evagorac/Terry/Assemblies/gasSpring.sldasm

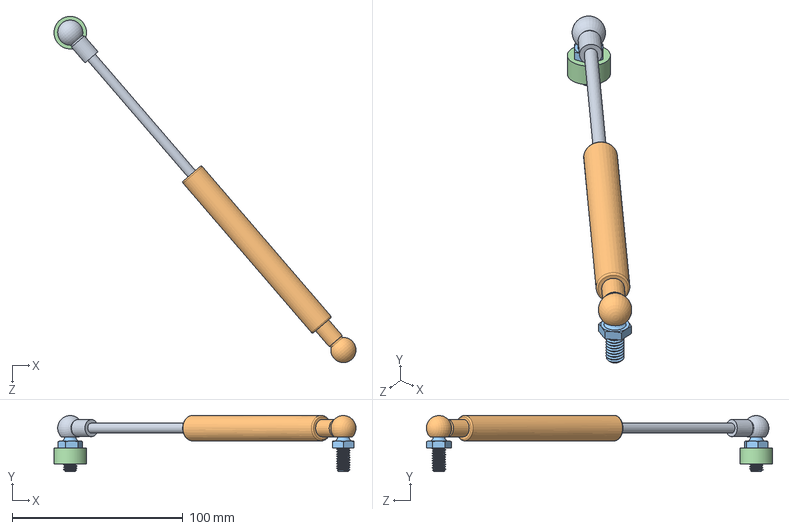
[picture p21: CAD file, 2020-08-20]
Assemblies/gasSpring.sldasm
176.8 x 33.0 x 202.7 mm
Combine2
Combine3
Combine1 x 2
92510A794_ALUM UNTHRD SPACER
