evagorac/Terry/Assemblies/TensionPillarJ4.sldasm

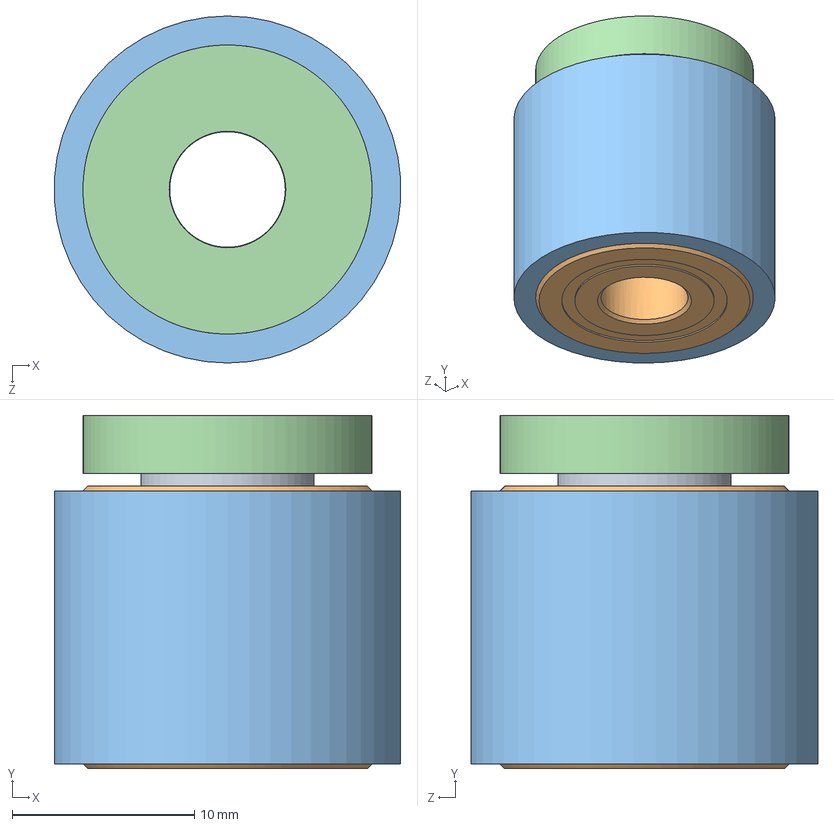
[picture p22: CAD file, 2020-08-20]
Assemblies/TensionPillarJ4.sldasm
19.0 x 19.4 x 19.1 mm
98019A228_MIL SPEC. 300 SERIES SS FLAT WASHER
60355K701_BALL BEARING x 2
Roller^TensionPillarJ4
92510A483_ALUM UNTHRD SPACER
