evagorac/Terry/Assemblies/gasSpring2.sldasm

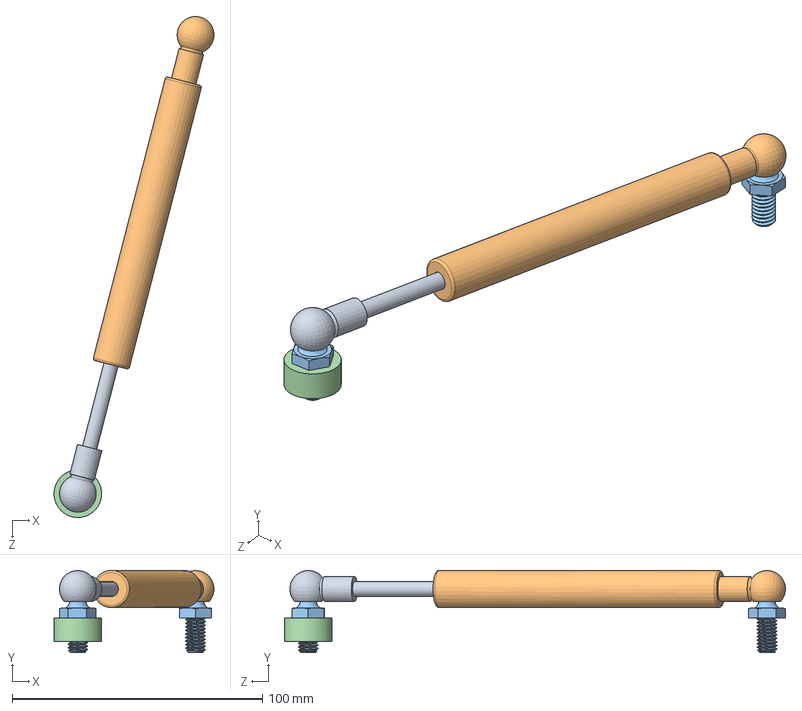
[picture p23: CAD file, 2020-08-20]
Assemblies/gasSpring2.sldasm
64.0 x 33.0 x 200.3 mm
Combine2
Combine3
Combine1 x 2
92510A794_ALUM UNTHRD SPACER
