evagorac/Terry/Parts/Pulleys/PulleyHubbed.SLDASM

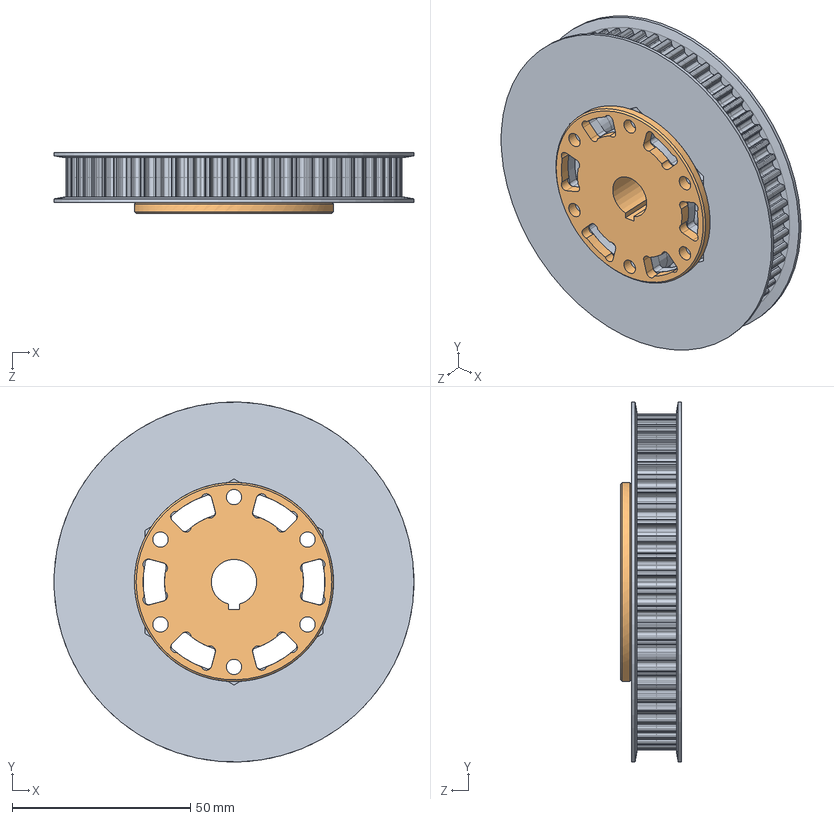
[picture p24: CAD file, 2020-08-20]
Parts/Pulleys/PulleyHubbed.SLDASM
101.0 x 101.0 x 17.2 mm
217-3200-001 Rev3.step x 2
1_2_ID_1_8_Keyway_Aluminum_VersaHub_217-2590 v1
