evagorac/Terry/Parts/Pulleys/60t_x_18mm_Wide_VersaPulley_Kit_HTD_5mm_VersaKeys_217-3200 v2.SLDASM

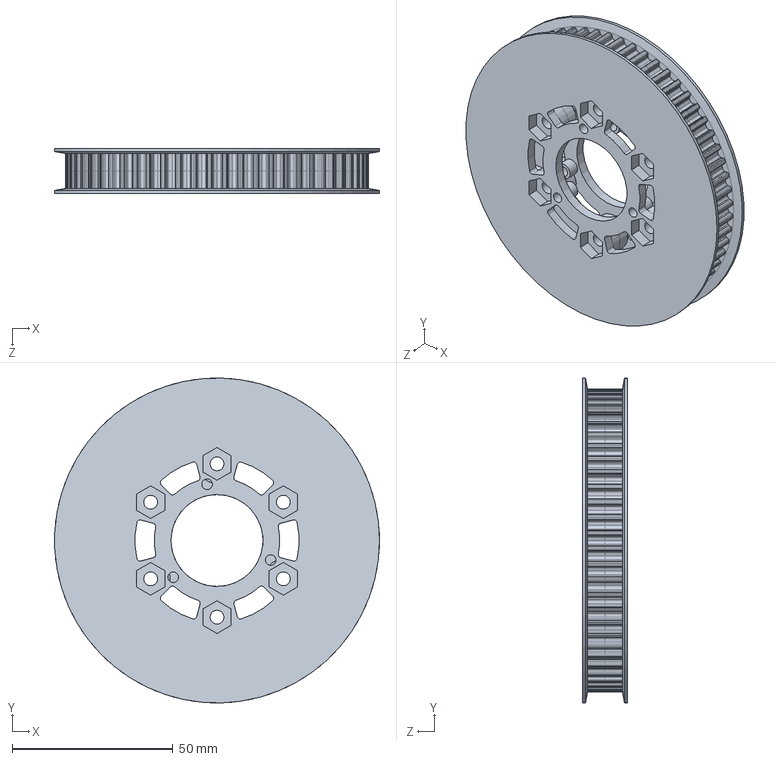
[picture p25: CAD file, 2020-08-20]
Parts/Pulleys/60t_x_18mm_Wide_VersaPulley_Kit_HTD_5mm_VersaKeys_217-3200 v2.SLDASM
101.0 x 101.0 x 14.0 mm
217-3200-001 Rev3.step x 2
