evagorac/Terry/STLS/Done/1MainMiterSpacer^Forearm.STL

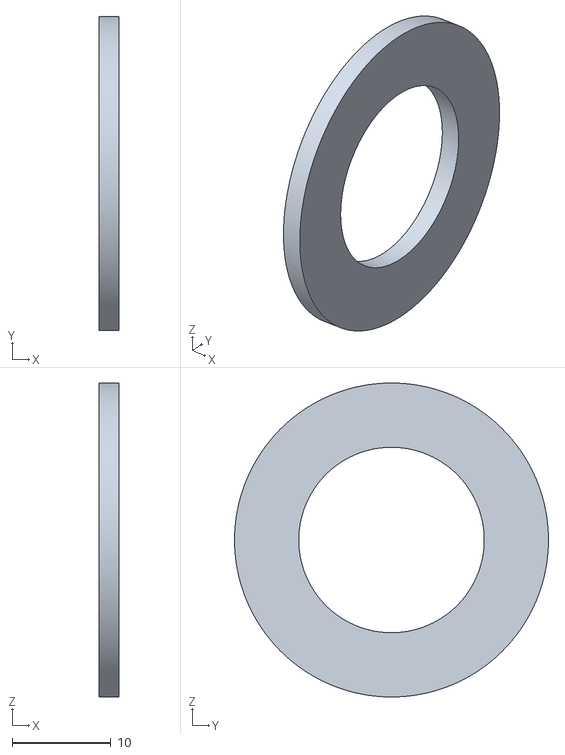
[picture p26: CAD file, 2020-08-20]
STLS/Done/1MainMiterSpacer^Forearm.STL
2.03 x 31.8 x 31.8
