evagorac/Terry/MillParts/Box.sldprt

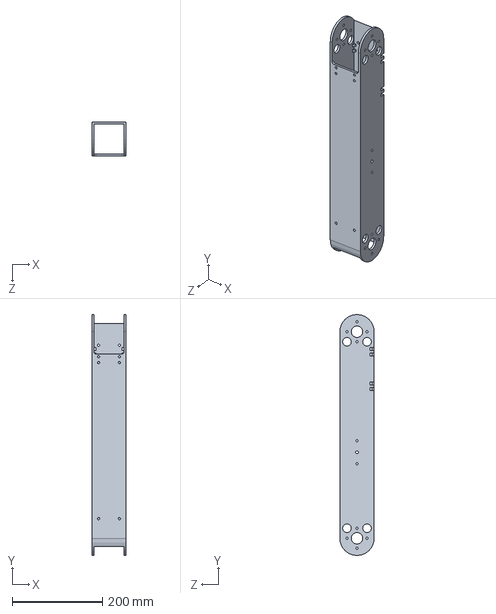
[picture p27: CAD file, 2021-02-25]
MillParts/Box.sldprt
76.2 x 533.4 x 76.2 mm
