evagorac/Terry/Parts/BBQ Bearing/8in.SLDPRT

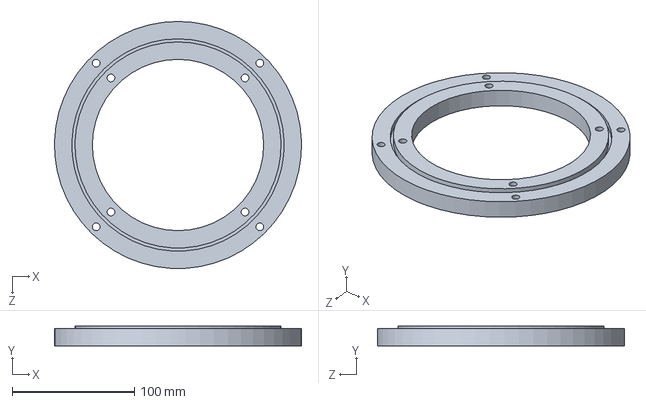
[picture p28: CAD file, 2020-08-20]
Parts/BBQ Bearing/8in.SLDPRT
201.9 x 16.0 x 202.0 mm
