evagorac/Terry/Parts/Limit/switch.SLDPRT

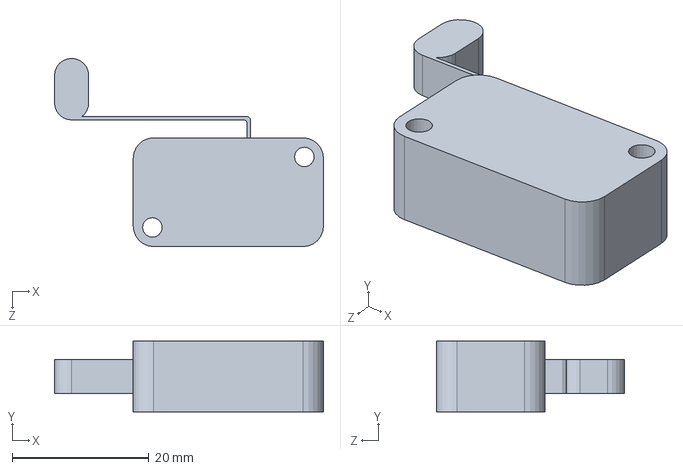
[picture p29: CAD file, 2020-08-20]
Parts/Limit/switch.SLDPRT
39.3 x 10.3 x 27.5 mm
