evagorac/Terry/Parts/MiscBodies/ShaftSupp^Shoulder.sldprt

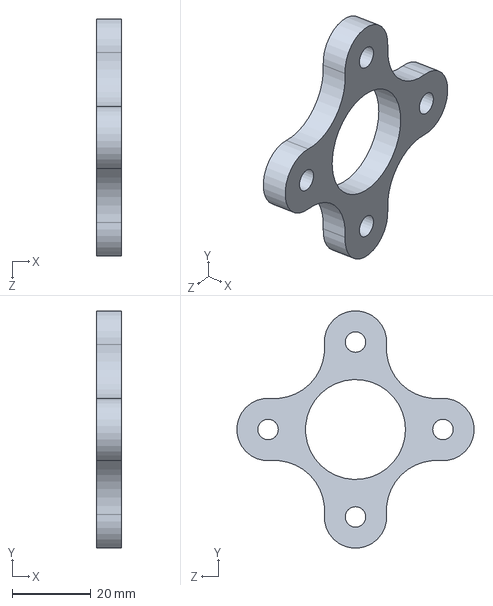
[picture p30: CAD file, 2021-02-25]
Parts/MiscBodies/ShaftSupp^Shoulder.sldprt
6.35 x 60.2 x 60.2 mm
