evagorac/Terry/Parts/Motors/Gearboxes/VersaPlanetary_CIM_Adapter_217-4018.SLDPRT

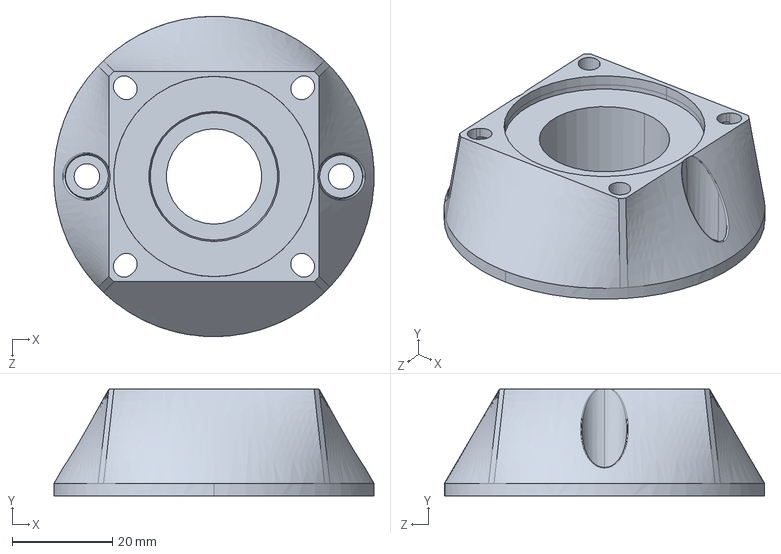
[picture p31: CAD file, 2020-08-20]
Parts/Motors/Gearboxes/VersaPlanetary_CIM_Adapter_217-4018.SLDPRT
63.9 x 21.4 x 64.0 mm
