evagorac/Terry/Parts/Pulleys/PulleyGenerator.SLDPRT

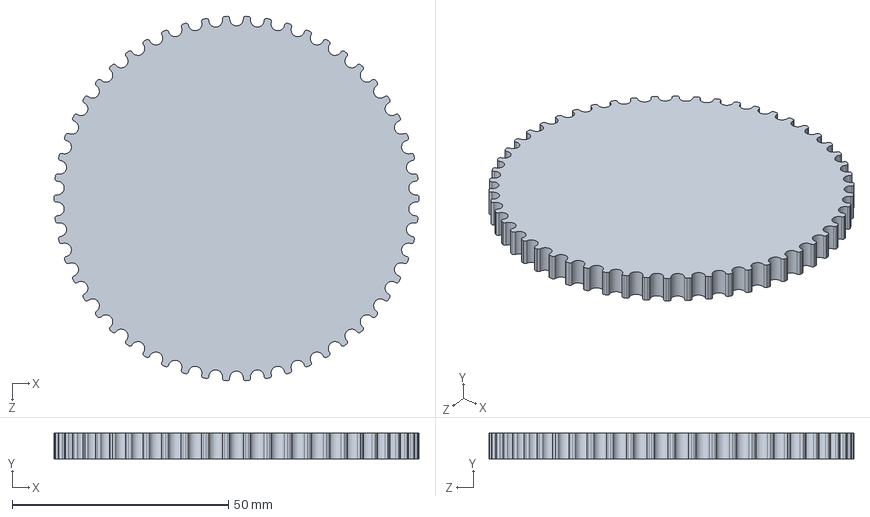
[picture p32: CAD file, 2021-02-25]
Parts/Pulleys/PulleyGenerator.SLDPRT
84.4 x 6.00 x 84.3 mm
