evagorac/Terry/Parts/VersaGussets/VersaFrame_Face_Bearing_Mount_217-4183.SLDPRT

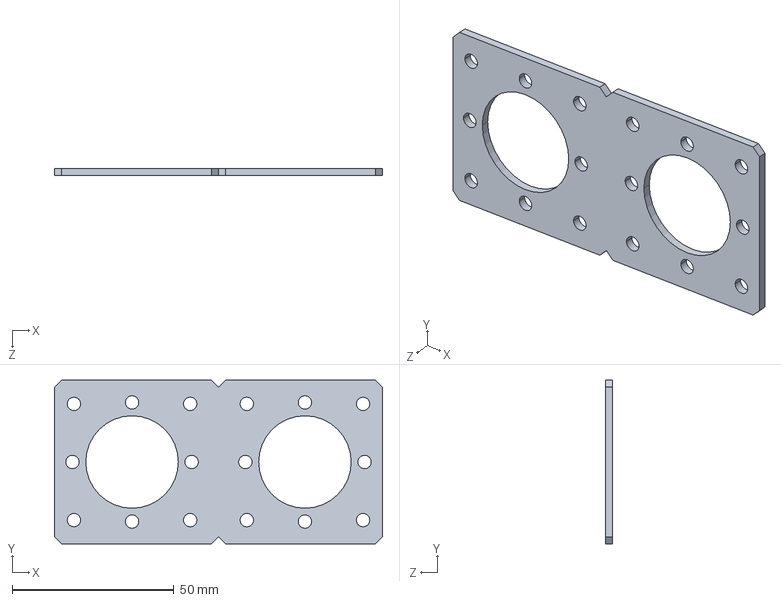
[picture p33: CAD file, 2020-08-20]
Parts/VersaGussets/VersaFrame_Face_Bearing_Mount_217-4183.SLDPRT
101.3 x 50.5 x 2.29 mm
