evagorac/Terry/Plates/Eighth/SidePlate1fix.sldprt

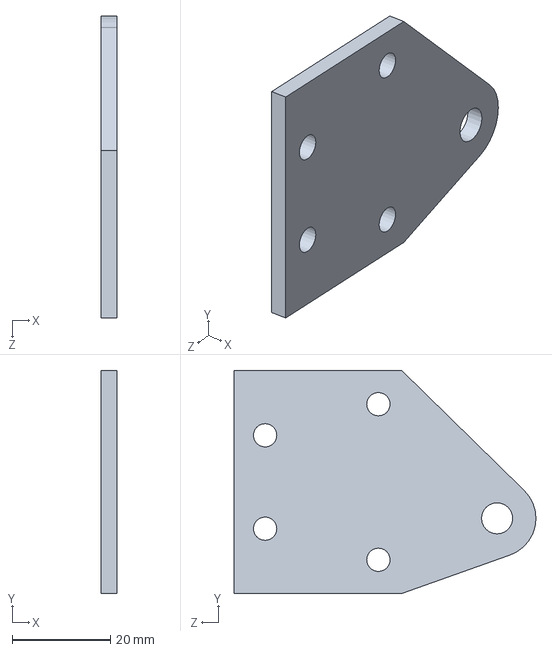
[picture p34: CAD file, 2020-12-14]
Plates/Eighth/SidePlate1fix.sldprt
3.17 x 45.5 x 61.6 mm
