evagorac/Terry/Plates/Quarter/J2Plate.sldprt

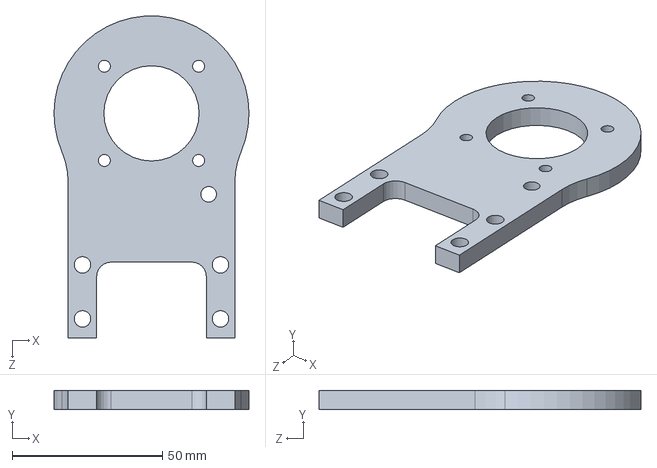
[picture p35: CAD file, 2020-08-20]
Plates/Quarter/J2Plate.sldprt
65.0 x 6.35 x 107.3 mm
