evagorac/Terry/STLS/Done/1Roller^TensionPillarJ3.STL

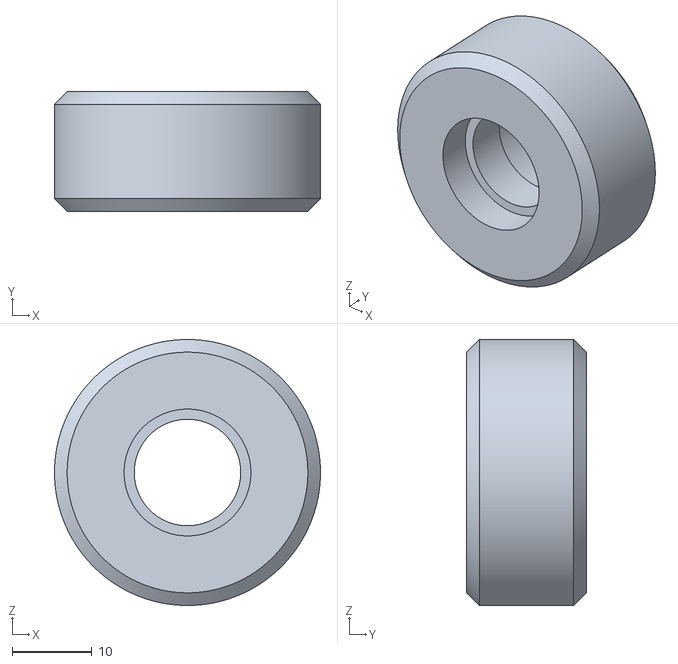
[picture p36: CAD file, 2020-08-20]
STLS/Done/1Roller^TensionPillarJ3.STL
33.3 x 15.0 x 33.3
