evagorac/Terry/STLS/Undone/2WristCover^Forearm.STL

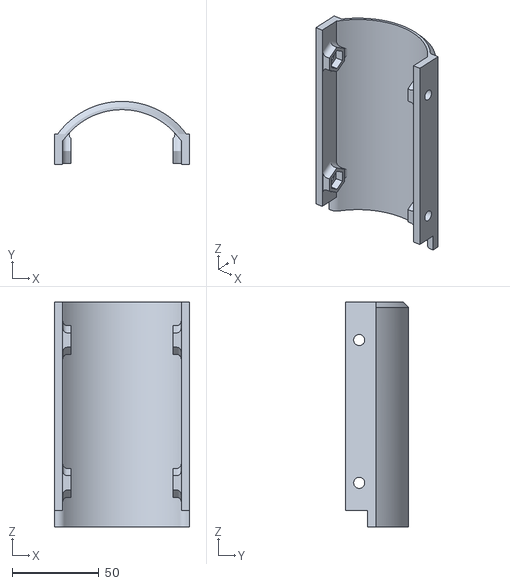
[picture p37: CAD file, 2020-08-20]
STLS/Undone/2WristCover^Forearm.STL
77.8 x 36.3 x 129.5
