evagorac/Terry/MillParts/HandPlate.sldprt

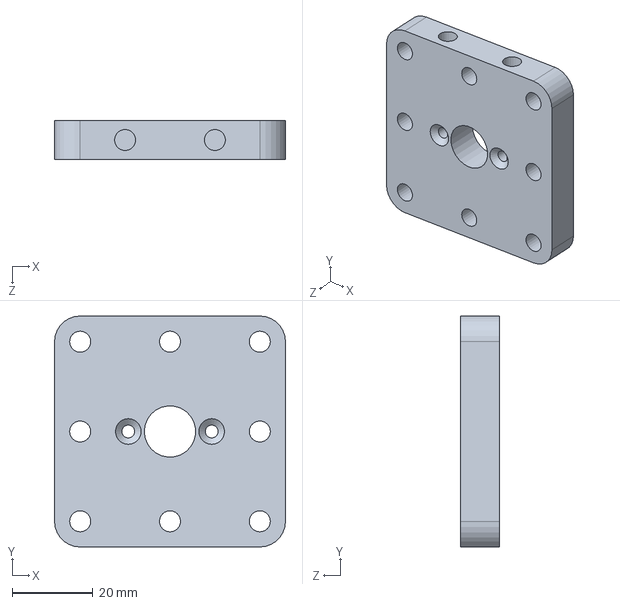
[picture p38: CAD file, 2021-02-25]
MillParts/HandPlate.sldprt
57.1 x 57.1 x 9.53 mm
