evagorac/Terry/Parts/Marker.step

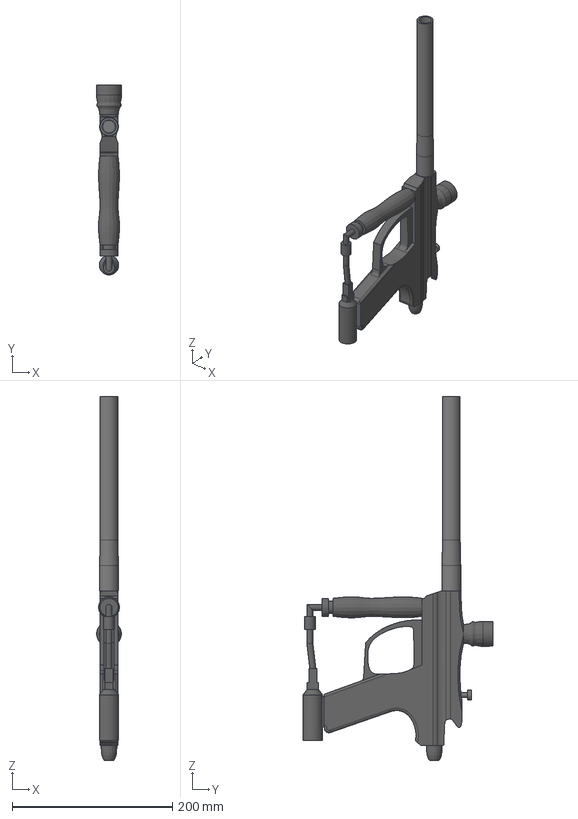
[picture p39: CAD file, 2021-02-25]
Parts/Marker.step
31.0 x 237.2 x 454.7 mm
Barrel
Delarin Bolt
