evagorac/Terry/Parts/MiscBodies/circularLineup.SLDPRT

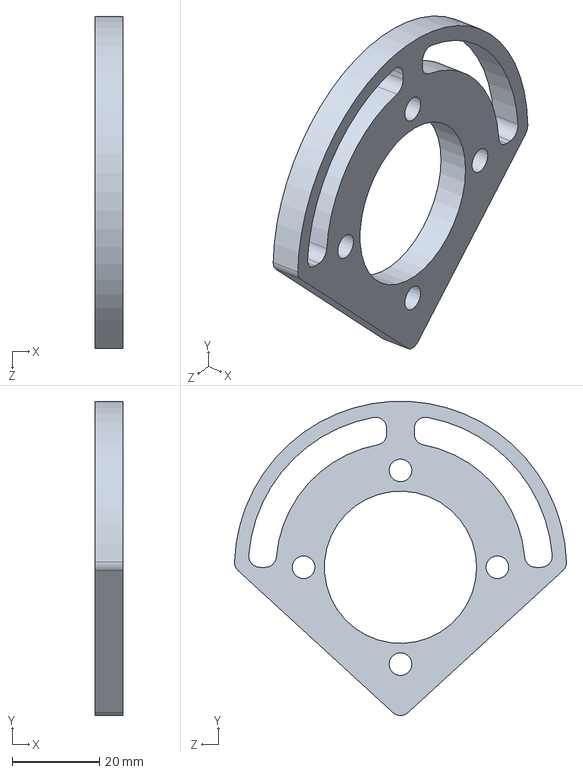
[picture p40: CAD file, 2020-08-20]
Parts/MiscBodies/circularLineup.SLDPRT
6.35 x 72.1 x 76.2 mm
