evagorac/Terry/Parts/Motors/Gearboxes/VersaPlanetary_CIM_Motor_Output_Shaft_Kit_217-2893.SLDPRT

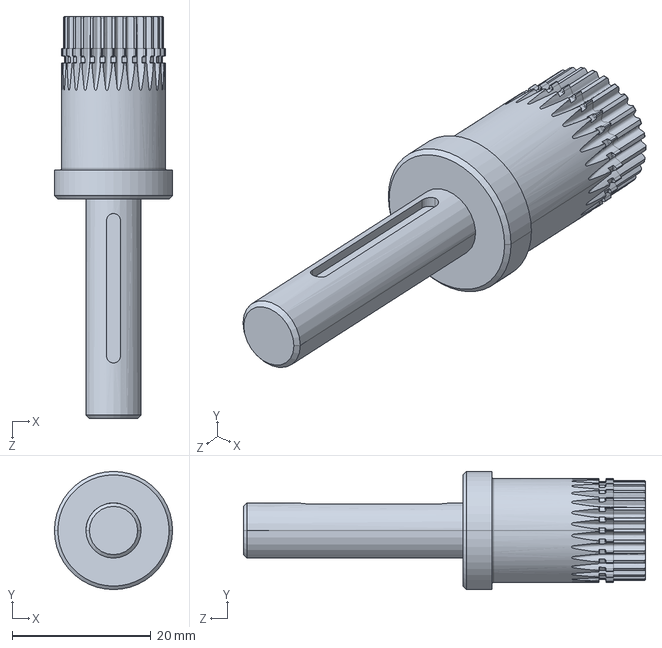
[picture p41: CAD file, 2020-08-20]
Parts/Motors/Gearboxes/VersaPlanetary_CIM_Motor_Output_Shaft_Kit_217-2893.SLDPRT
17.0 x 17.0 x 57.8 mm
