evagorac/Terry/Parts/Pulleys/J1Pulley.SLDPRT

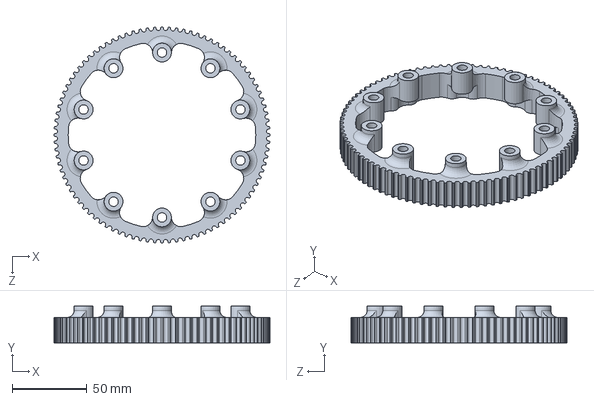
[picture p42: CAD file, 2020-10-19]
Parts/Pulleys/J1Pulley.SLDPRT
144.9 x 24.5 x 144.9 mm
