evagorac/Terry/Parts/Rails/J3MGN12C.sldprt

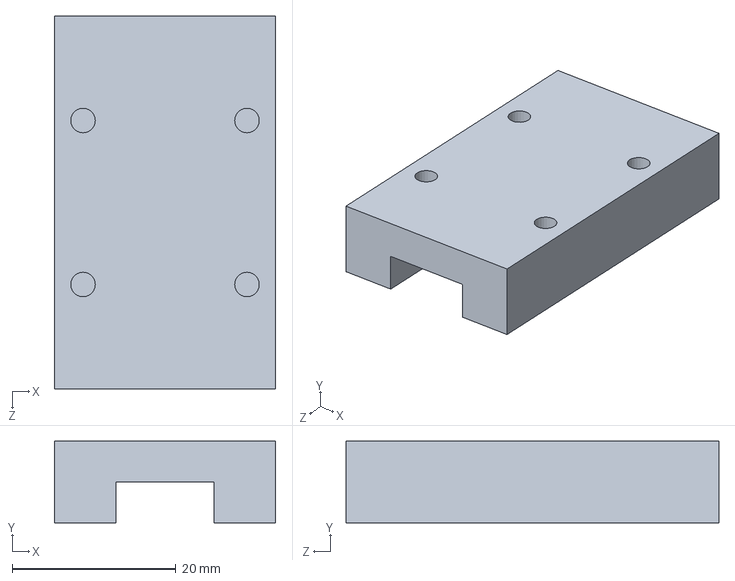
[picture p43: CAD file, 2020-08-20]
Parts/Rails/J3MGN12C.sldprt
27.0 x 10.0 x 45.5 mm
