evagorac/Terry/Plates/Quarter/J3Plate.sldprt

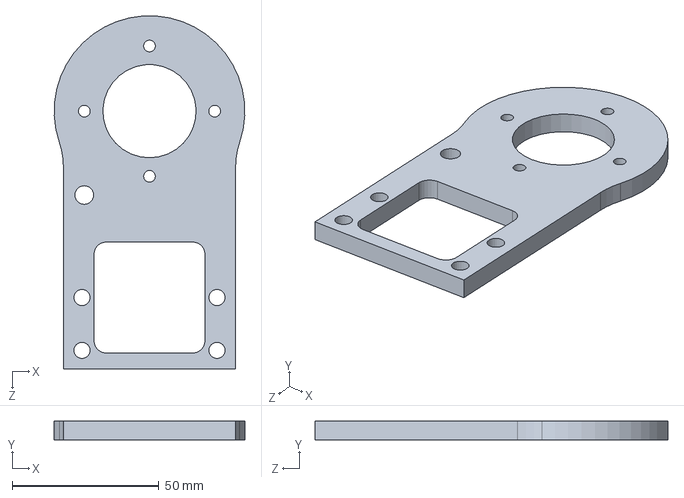
[picture p44: CAD file, 2020-08-20]
Plates/Quarter/J3Plate.sldprt
64.9 x 6.35 x 120.3 mm
