evagorac/Terry/Plates/ThreeEighths/SideTurretPlate.sldprt

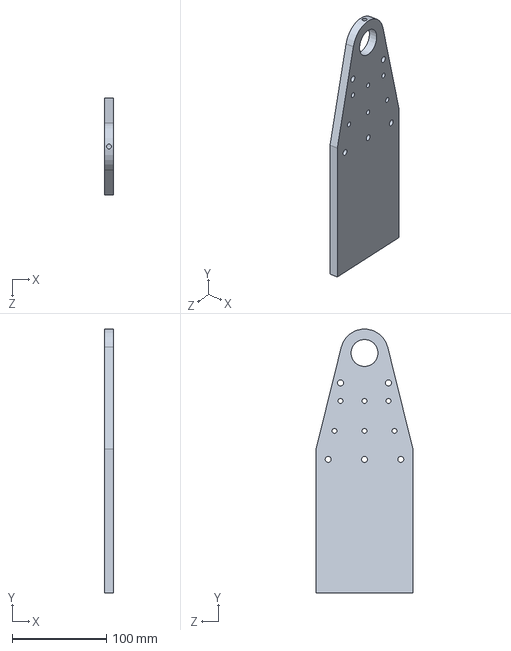
[picture p45: CAD file, 2020-08-20]
Plates/ThreeEighths/SideTurretPlate.sldprt
9.53 x 279.6 x 102.6 mm
