evagorac/Terry/STLS/Done/4Body^192kvMotorEncoded.STL

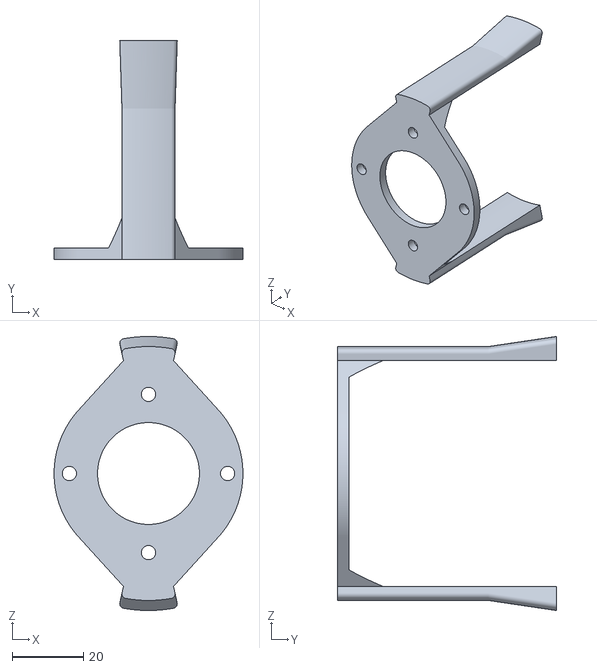
[picture p46: CAD file, 2020-08-20]
STLS/Done/4Body^192kvMotorEncoded.STL
53.0 x 61.4 x 76.9
