evagorac/Terry/Parts/MiscBodies/BigPlateLineup.sldprt

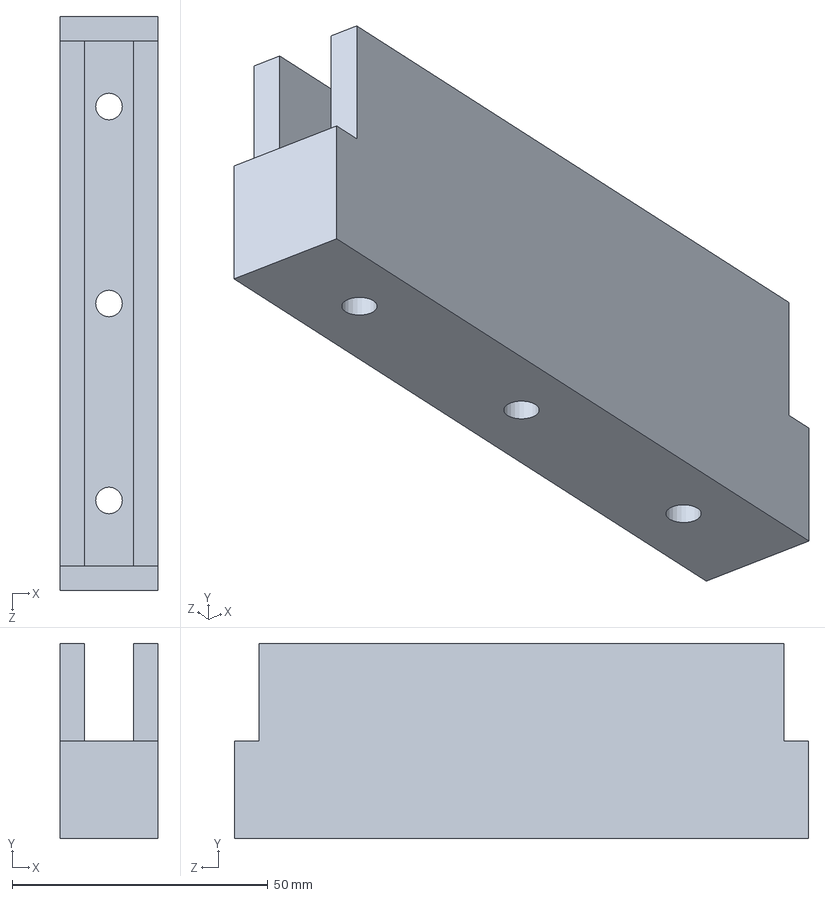
[picture p47: CAD file, 2020-08-20]
Parts/MiscBodies/BigPlateLineup.sldprt
19.0 x 38.1 x 112.1 mm
