evagorac/Terry/Parts/Motors/BetterKEDA.SLDPRT

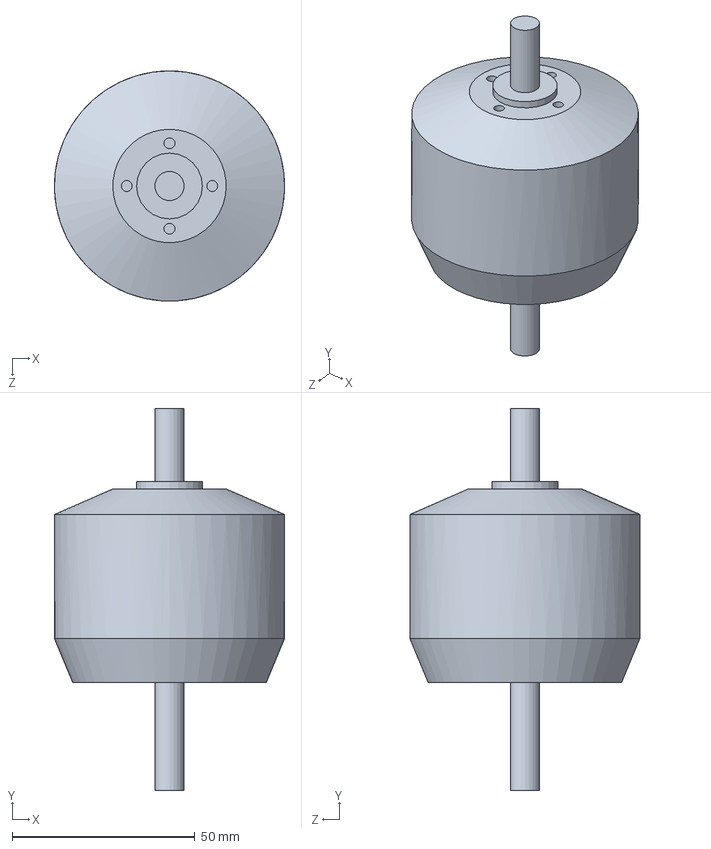
[picture p48: CAD file, 2020-08-20]
Parts/Motors/BetterKEDA.SLDPRT
63.0 x 104.5 x 63.0 mm
