evagorac/Terry/Plates/Eighth/WristSidePlate.sldprt

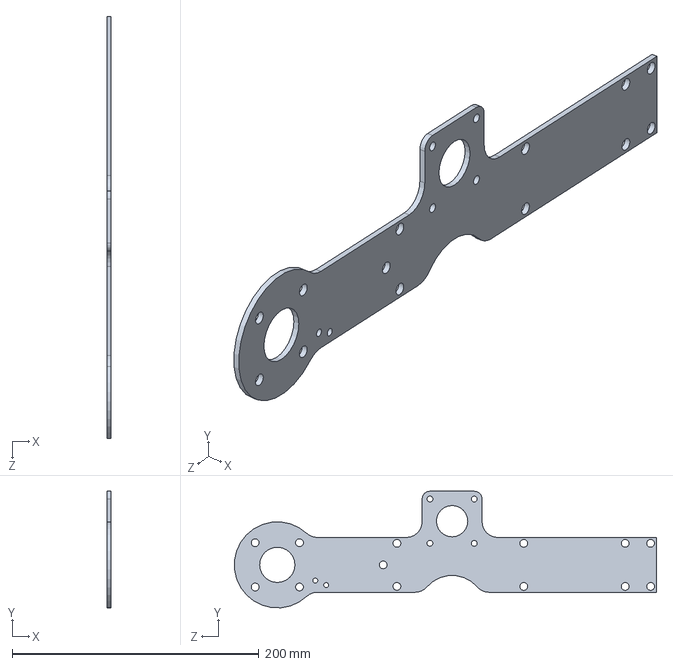
[picture p49: CAD file, 2020-08-20]
Plates/Eighth/WristSidePlate.sldprt
3.18 x 94.5 x 342.1 mm
