evagorac/Terry/Plates/Quarter/BotTurretPlate.sldprt

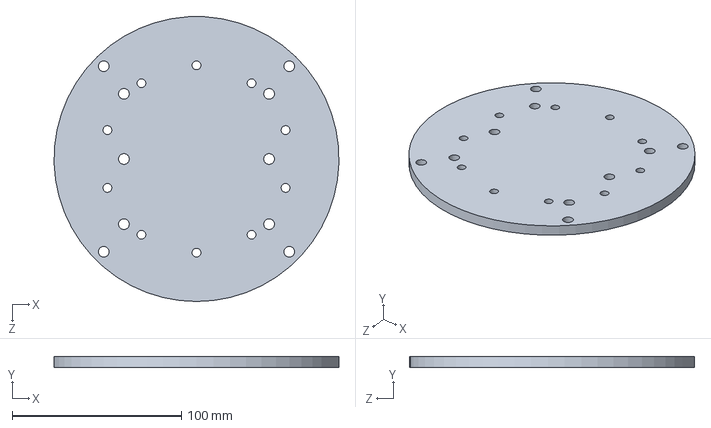
[picture p50: CAD file, 2020-08-20]
Plates/Quarter/BotTurretPlate.sldprt
168.3 x 6.35 x 168.3 mm
