evagorac/Terry/STLS/Done/1ThrustBase^Forearm.STL

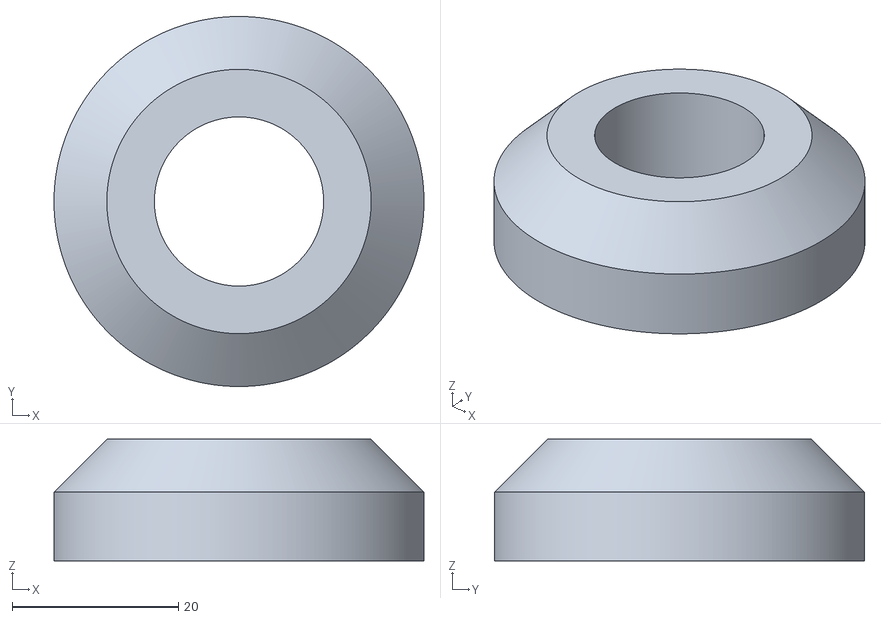
[picture p51: CAD file, 2020-08-20]
STLS/Done/1ThrustBase^Forearm.STL
44.5 x 44.5 x 14.6
