evagorac/Terry/MillParts/WristHub.sldprt

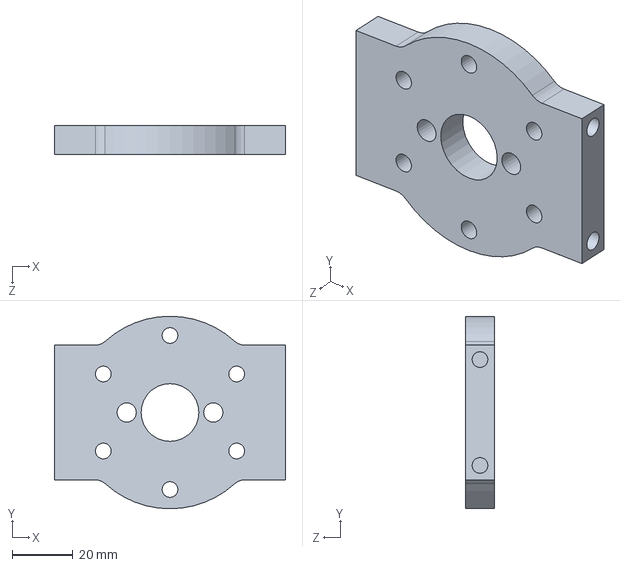
[picture p52: CAD file, 2020-08-20]
MillParts/WristHub.sldprt
76.2 x 63.5 x 9.52 mm
