evagorac/Terry/Parts/Motors/EXTENDED SHAFT KEDA 56-63 195KV Brushless Outrunner 6S 1500W v2 v2.step

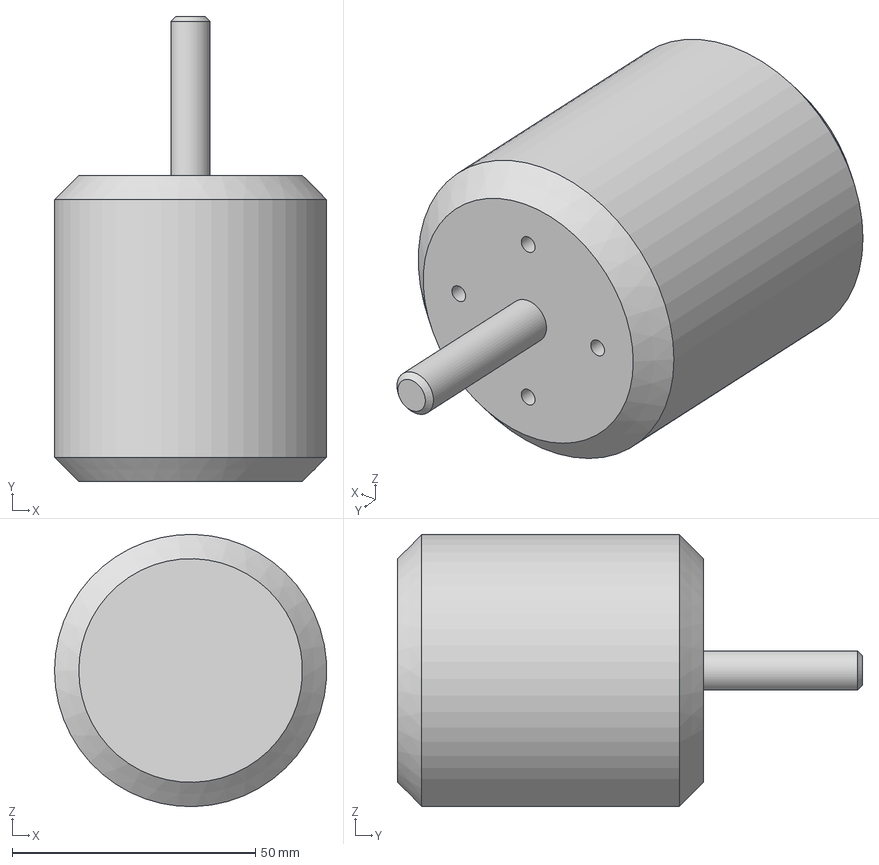
[picture p53: CAD file, 2020-08-20]
Parts/Motors/EXTENDED SHAFT KEDA 56-63 195KV Brushless Outrunner 6S 1500W v2 v2.step
55.9 x 95.7 x 56.0 mm
