evagorac/Terry/Parts/Pulleys/15Tpulley.SLDPRT

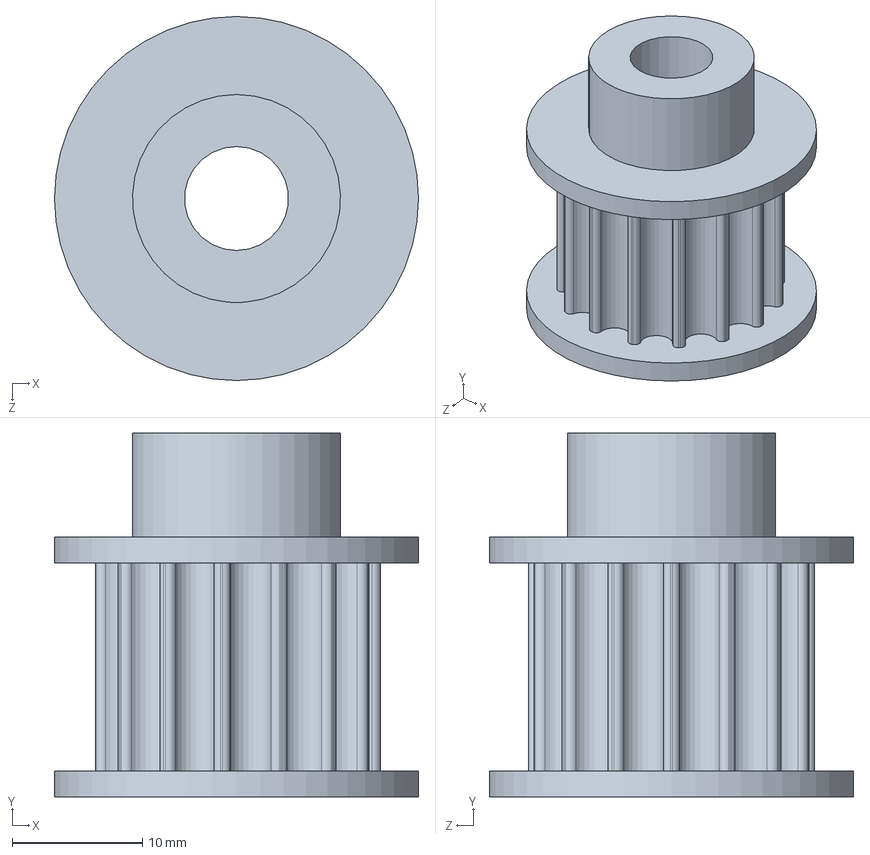
[picture p54: CAD file, 2020-08-20]
Parts/Pulleys/15Tpulley.SLDPRT
28.0 x 28.0 x 28.0 mm
