evagorac/Terry/Plates/Eighth/PulleySupportPlate.sldprt

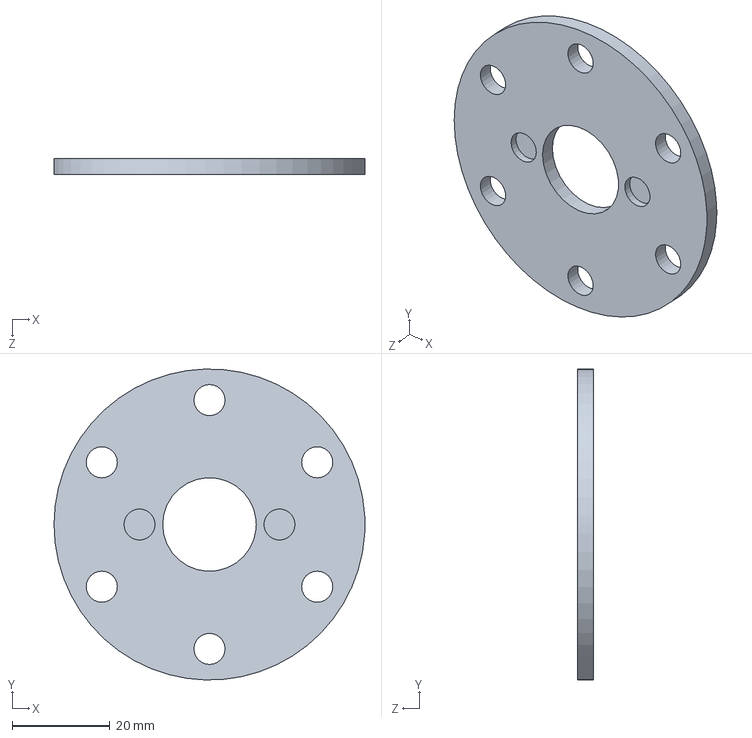
[picture p55: CAD file, 2020-08-20]
Plates/Eighth/PulleySupportPlate.sldprt
63.5 x 63.5 x 3.18 mm
