evagorac/Terry/Plates/Quarter/Sole.sldprt

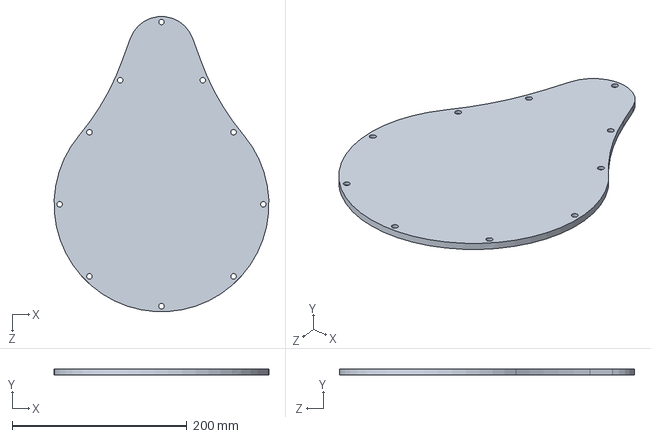
[picture p56: CAD file, 2020-08-20]
Plates/Quarter/Sole.sldprt
245.9 x 6.35 x 338.0 mm
