evagorac/Terry/STLS/Done/1Trigger^Shoulder.STL

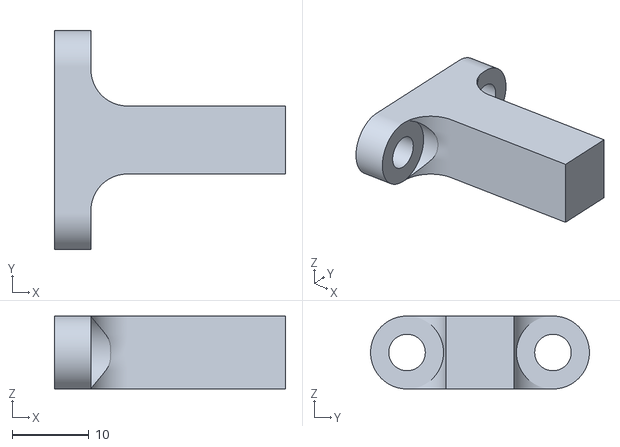
[picture p57: CAD file, 2020-08-20]
STLS/Done/1Trigger^Shoulder.STL
30.2 x 28.6 x 9.53
