evagorac/Terry/Parts/Motors/PROPDRIVE v2 5060 380KV Brushless Outrunner Motor.SLDPRT

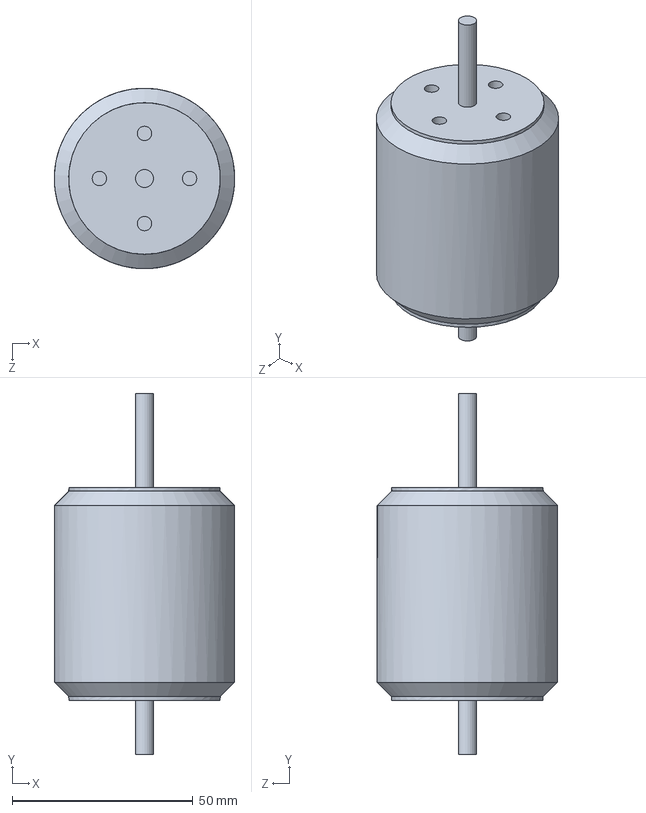
[picture p58: CAD file, 2020-08-20]
Parts/Motors/PROPDRIVE v2 5060 380KV Brushless Outrunner Motor.SLDPRT
50.0 x 100.0 x 50.0 mm
