evagorac/Terry/Parts/Pulleys/1_2_ID_1_8_Keyway_Aluminum_VersaHub_217-2590 v1.SLDPRT

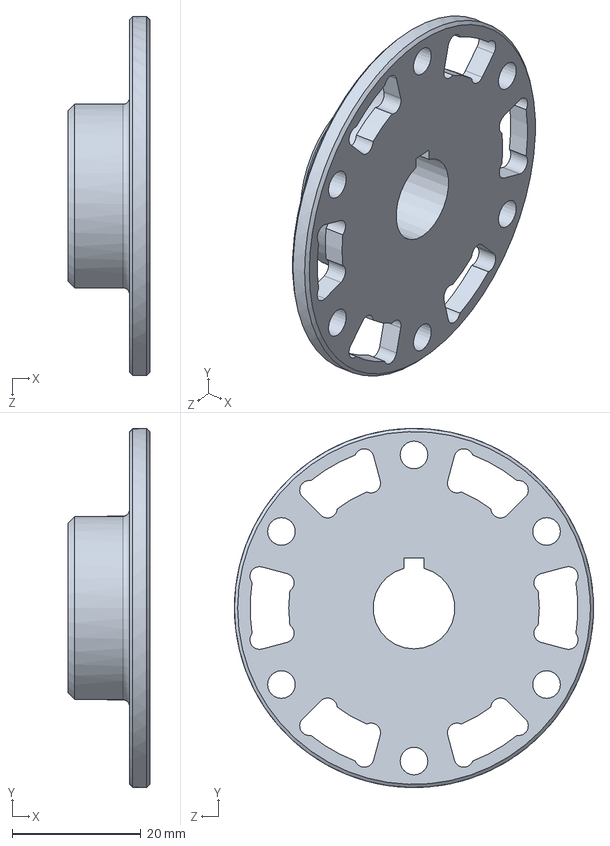
[picture p59: CAD file, 2020-08-20]
Parts/Pulleys/1_2_ID_1_8_Keyway_Aluminum_VersaHub_217-2590 v1.SLDPRT
12.7 x 55.9 x 55.9 mm
