evagorac/Terry/Plates/ThreeEighths/SidePlate.sldprt

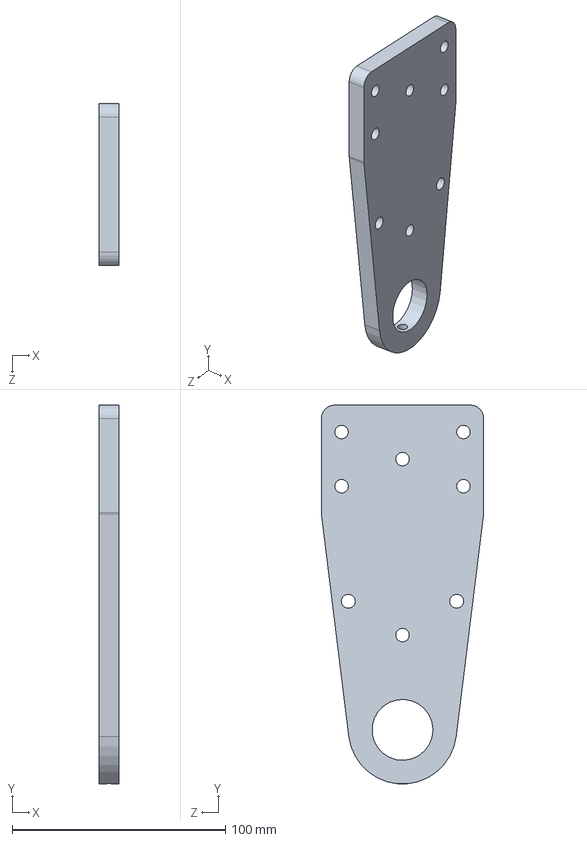
[picture p60: CAD file, 2020-08-20]
Plates/ThreeEighths/SidePlate.sldprt
9.53 x 177.8 x 76.2 mm
