evagorac/Terry/STLS/Done/2BKSpacer^Shoulder.STL

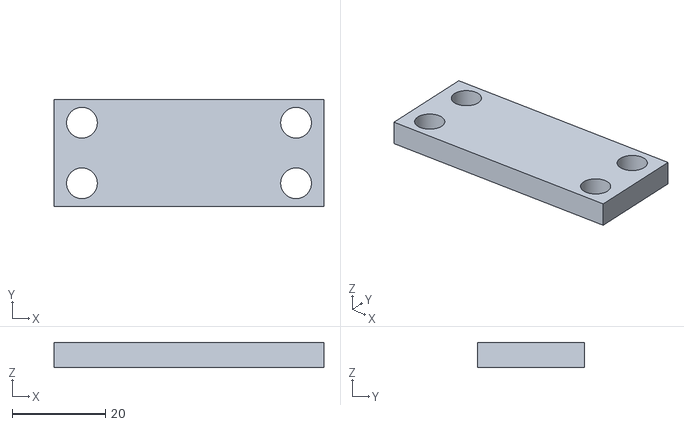
[picture p61: CAD file, 2020-08-20]
STLS/Done/2BKSpacer^Shoulder.STL
58.0 x 23.0 x 5.40
