evagorac/Terry/Parts/Pulleys/30Tpulley.SLDPRT

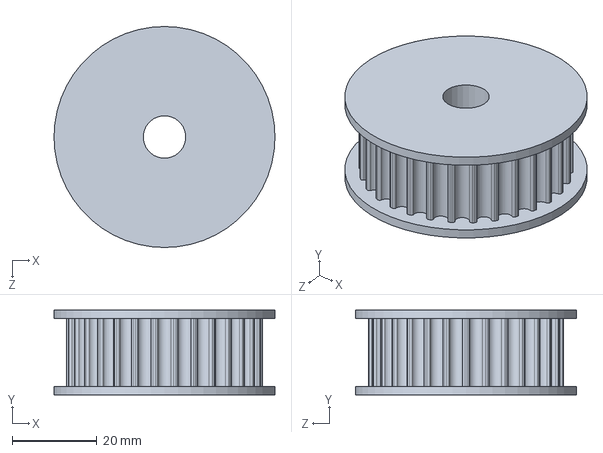
[picture p62: CAD file, 2020-08-20]
Parts/Pulleys/30Tpulley.SLDPRT
52.0 x 20.0 x 52.0 mm
