evagorac/Terry/Plates/Quarter/TopTurretPlate.sldprt

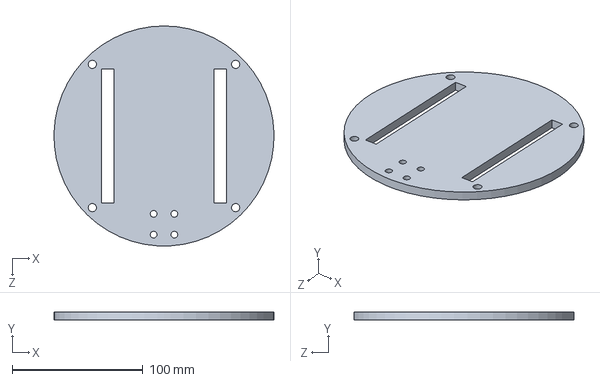
[picture p63: CAD file, 2020-08-20]
Plates/Quarter/TopTurretPlate.sldprt
168.3 x 6.35 x 168.3 mm
