evagorac/Terry/Plates/ThreeEighths/WristHub.sldprt

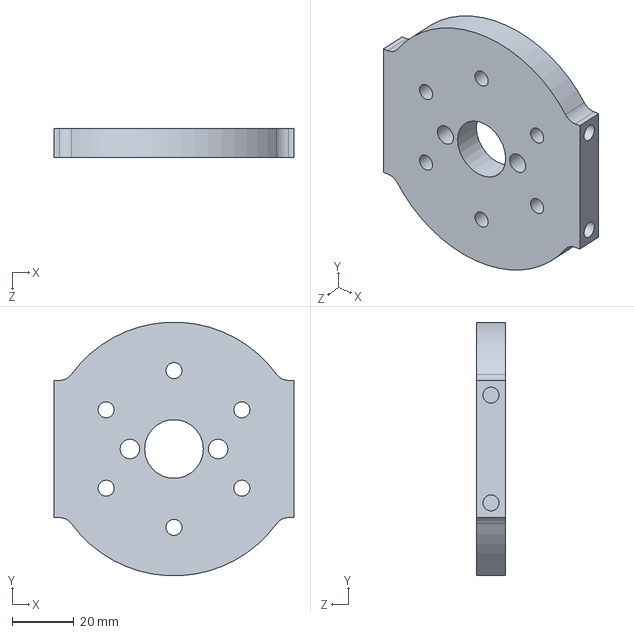
[picture p64: CAD file, 2020-08-20]
Plates/ThreeEighths/WristHub.sldprt
77.8 x 82.1 x 9.53 mm
