evagorac/Terry/STLS/Done/1BotTurretHousing^Base.STL

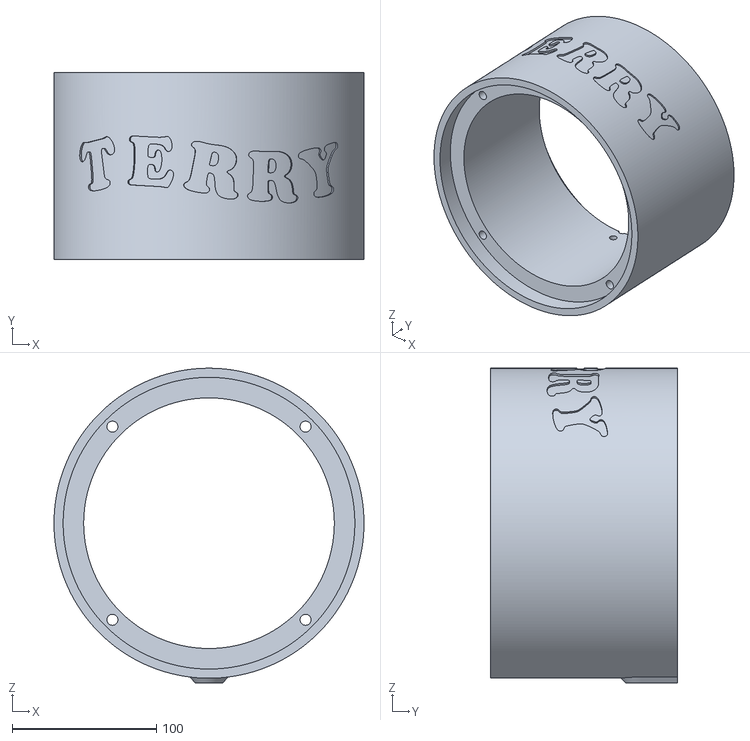
[picture p65: CAD file, 2020-08-20]
STLS/Done/1BotTurretHousing^Base.STL
214.7 x 129.6 x 217.9
