evagorac/Terry/Plates/Eighth/BasePlate.sldprt

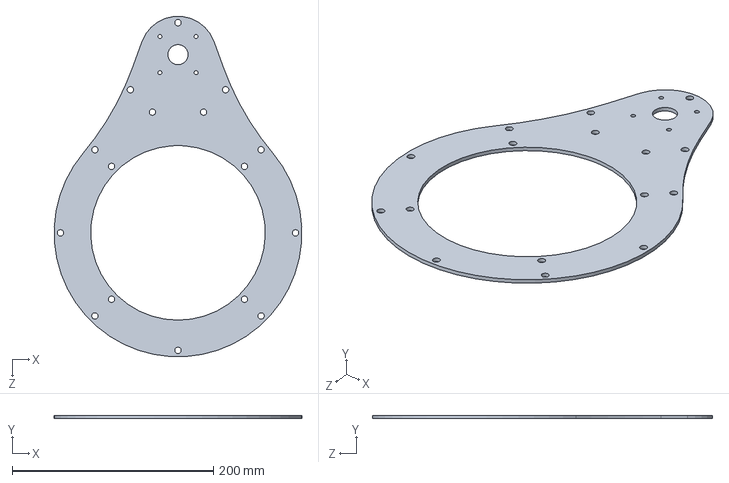
[picture p66: CAD file, 2020-08-20]
Plates/Eighth/BasePlate.sldprt
245.9 x 3.17 x 337.8 mm
