evagorac/Terry/Plates/Quarter/ShaftSupp.sldprt

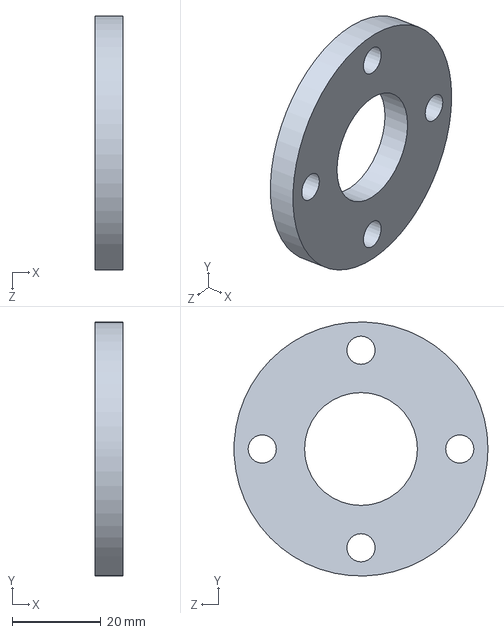
[picture p67: CAD file, 2020-08-20]
Plates/Quarter/ShaftSupp.sldprt
6.35 x 57.1 x 57.2 mm
