evagorac/Terry/Plates/ThreeEighths/TopBrace.sldprt

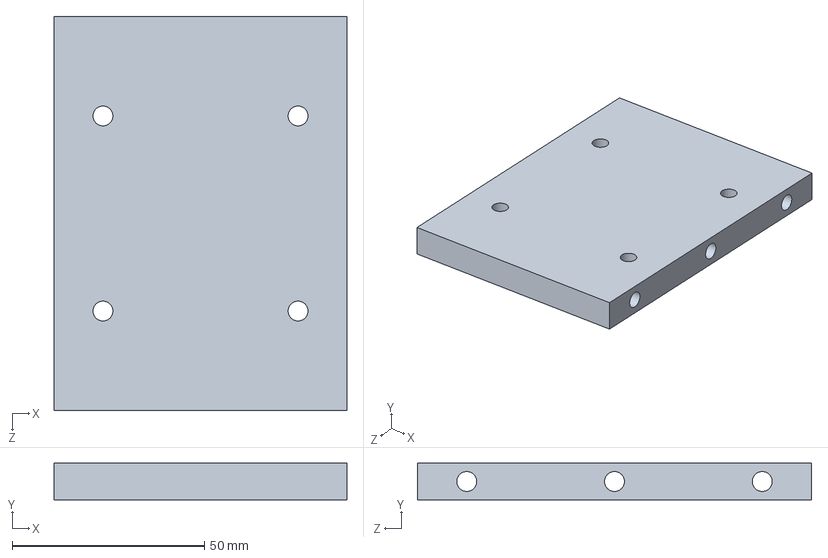
[picture p68: CAD file, 2020-08-20]
Plates/ThreeEighths/TopBrace.sldprt
76.2 x 9.52 x 102.6 mm
