evagorac/Terry/STLS/Done/1WristBase^Forearm.STL

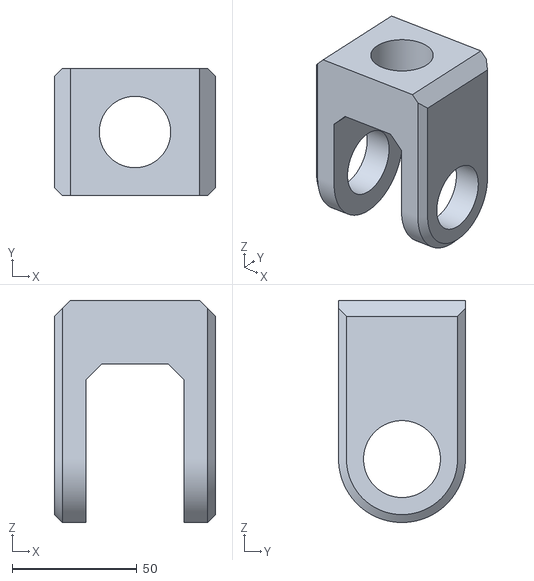
[picture p69: CAD file, 2020-08-20]
STLS/Done/1WristBase^Forearm.STL
64.5 x 50.8 x 88.9
