evagorac/Terry/Plates/Quarter/PivotPlate.sldprt

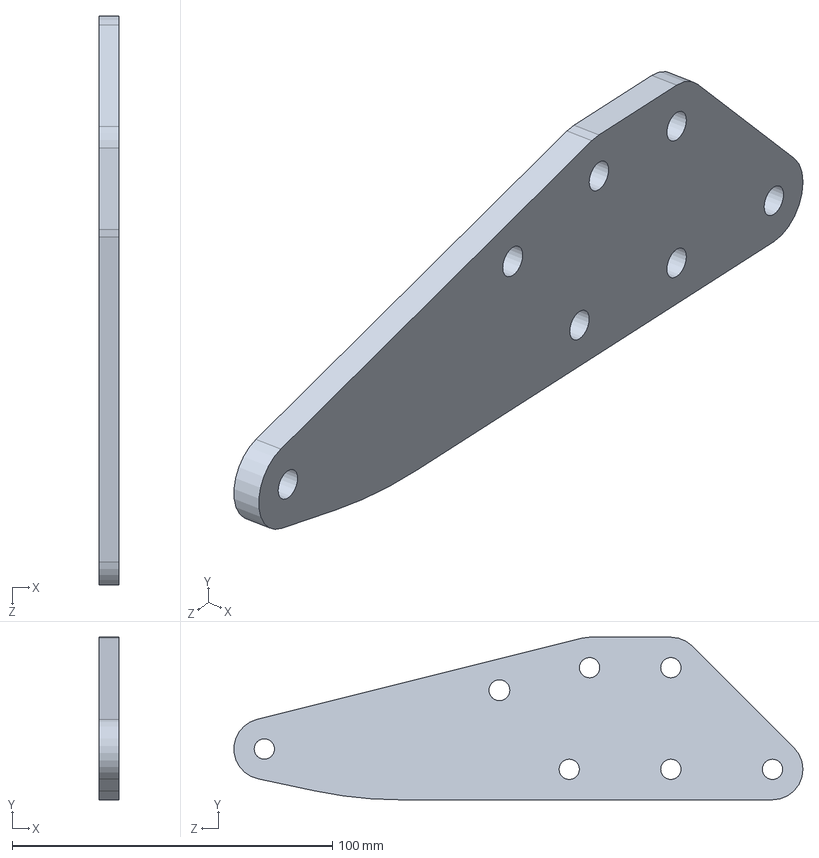
[picture p70: CAD file, 2020-08-20]
Plates/Quarter/PivotPlate.sldprt
6.35 x 50.8 x 177.7 mm
