evagorac/Terry/STLS/Done/1BFSpacerWSwitchMountPlate^Shoulder.STL

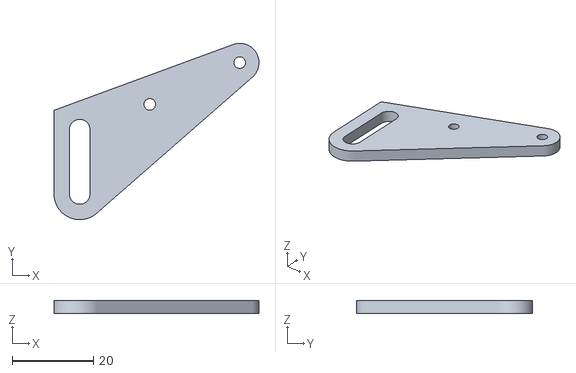
[picture p71: CAD file, 2020-08-20]
STLS/Done/1BFSpacerWSwitchMountPlate^Shoulder.STL
50.6 x 43.5 x 3.17
