evagorac/Terry/Plates/Eighth/SidePlate2.sldprt

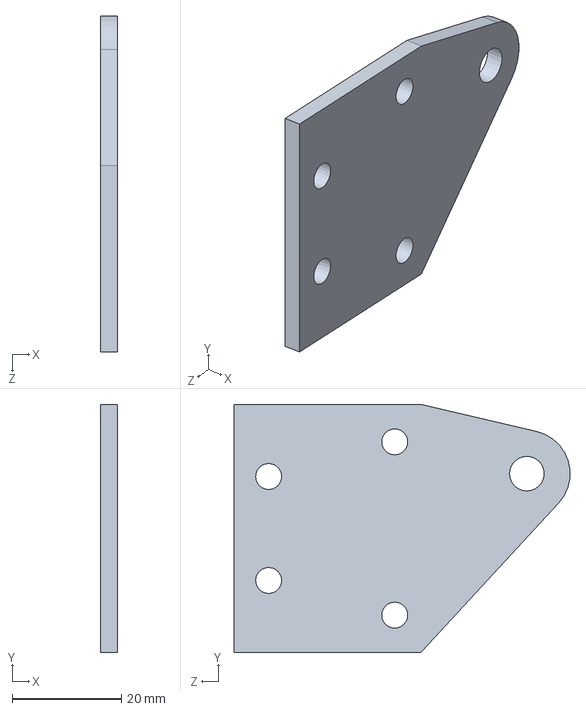
[picture p72: CAD file, 2020-08-20]
Plates/Eighth/SidePlate2.sldprt
3.17 x 45.5 x 61.6 mm
