evagorac/Terry/Plates/Quarter/J4MotorPlate.sldprt

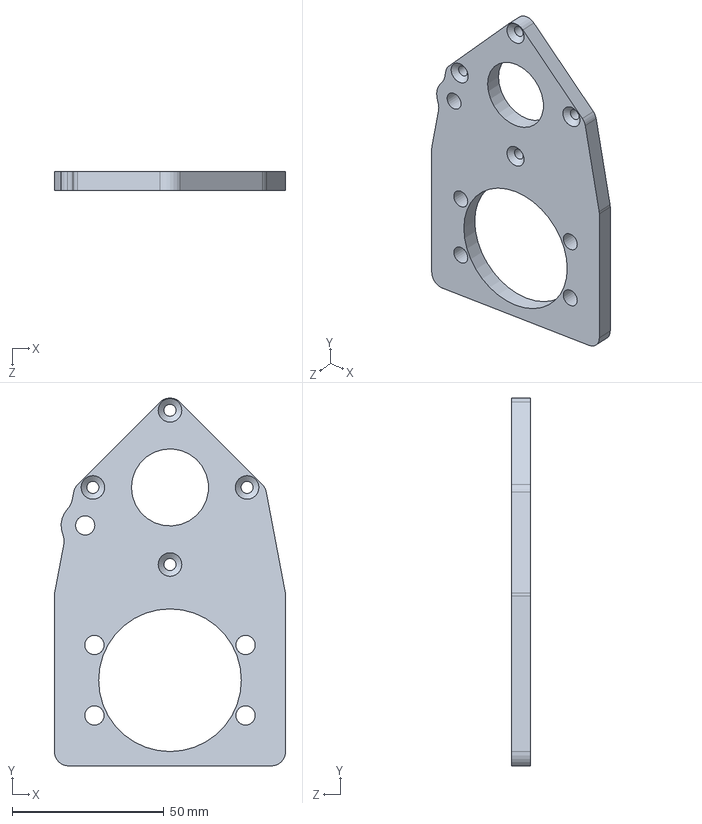
[picture p73: CAD file, 2020-08-20]
Plates/Quarter/J4MotorPlate.sldprt
76.2 x 121.2 x 6.35 mm
