evagorac/Terry/STLS/Done/1SwitchTripper^Base.STL

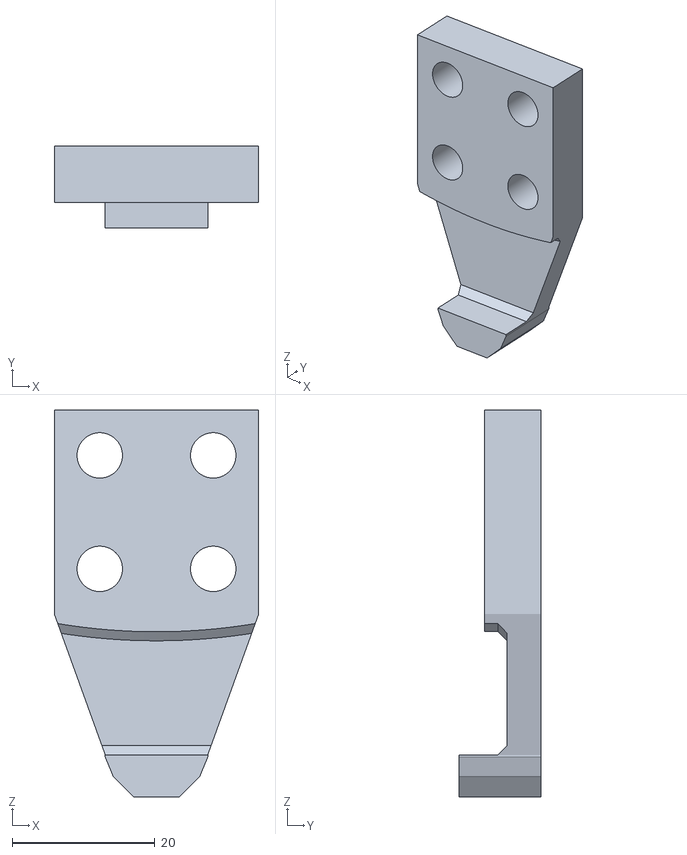
[picture p74: CAD file, 2020-08-20]
STLS/Done/1SwitchTripper^Base.STL
28.6 x 11.5 x 54.1
