evagorac/Terry/Parts/Pulleys/J4Pulley.SLDPRT

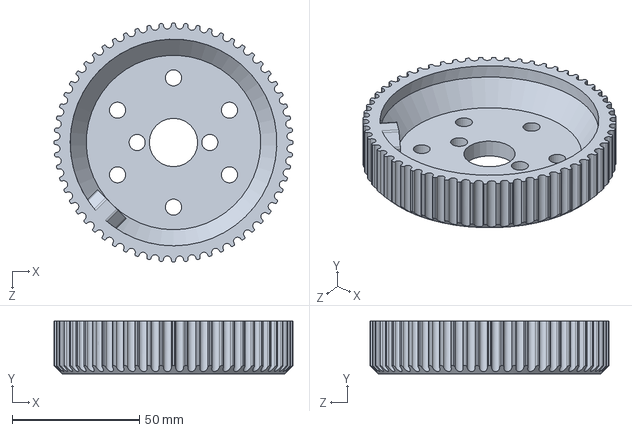
[picture p75: CAD file, 2020-08-20]
Parts/Pulleys/J4Pulley.SLDPRT
94.0 x 20.7 x 94.0 mm
