evagorac/Terry/Plates/Eighth/Bendy.sldprt

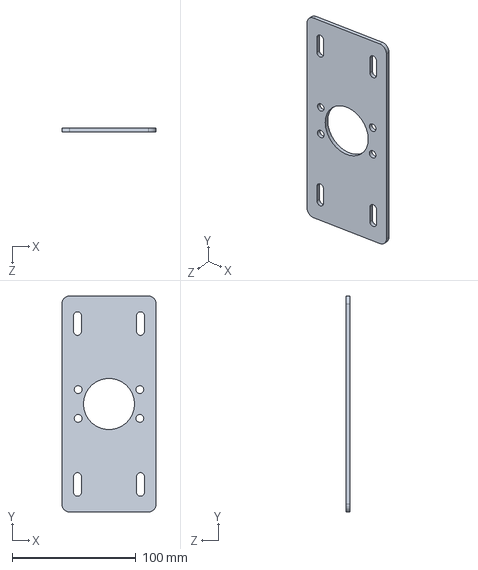
[picture p76: CAD file, 2020-08-20]
Plates/Eighth/Bendy.sldprt
76.2 x 174.3 x 3.18 mm
