evagorac/Terry/Plates/Quarter/BackSidePlate.sldprt

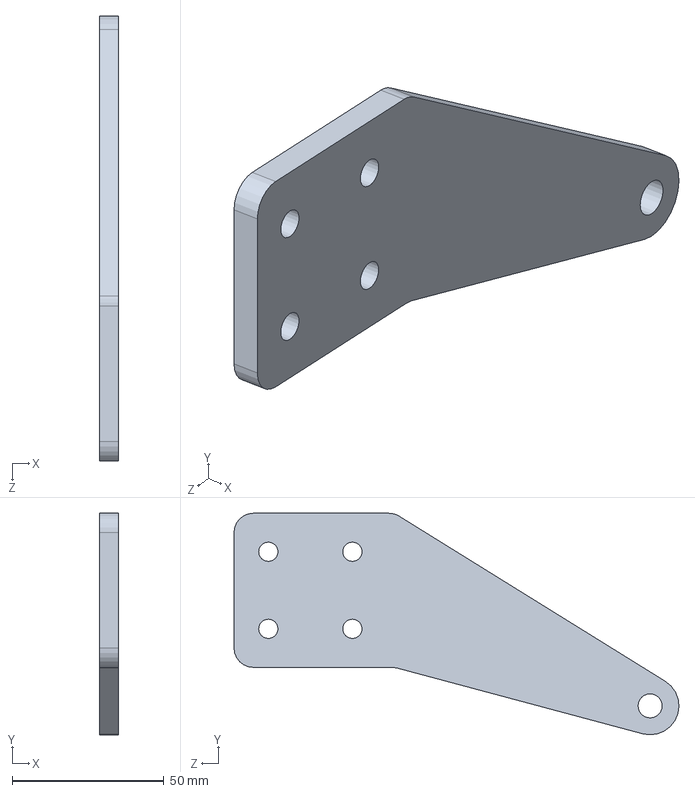
[picture p77: CAD file, 2020-08-20]
Plates/Quarter/BackSidePlate.sldprt
6.35 x 73.0 x 146.7 mm
