evagorac/Terry/STLS/Done/1J5SwitchMount^Forearm.STL

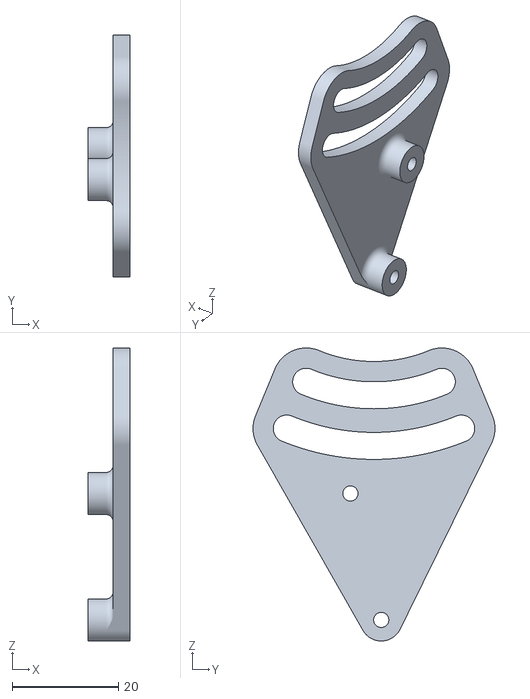
[picture p78: CAD file, 2020-08-20]
STLS/Done/1J5SwitchMount^Forearm.STL
7.84 x 45.5 x 55.1
