evagorac/Terry/Plates/Eighth/CarriagePlate.sldprt

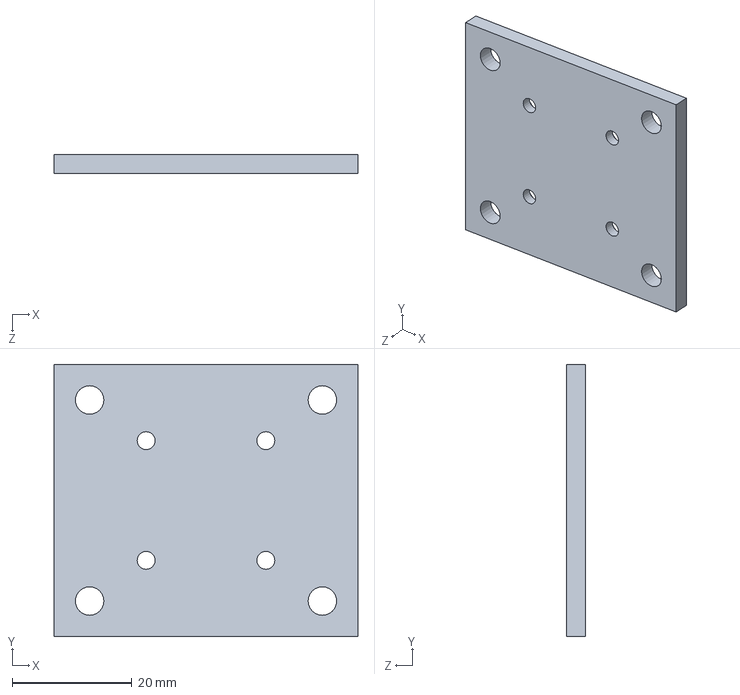
[picture p79: CAD file, 2020-08-20]
Plates/Eighth/CarriagePlate.sldprt
50.8 x 45.5 x 3.17 mm
