evagorac/Terry/STLS/Done/2BearingSpacer^Forearm.STL

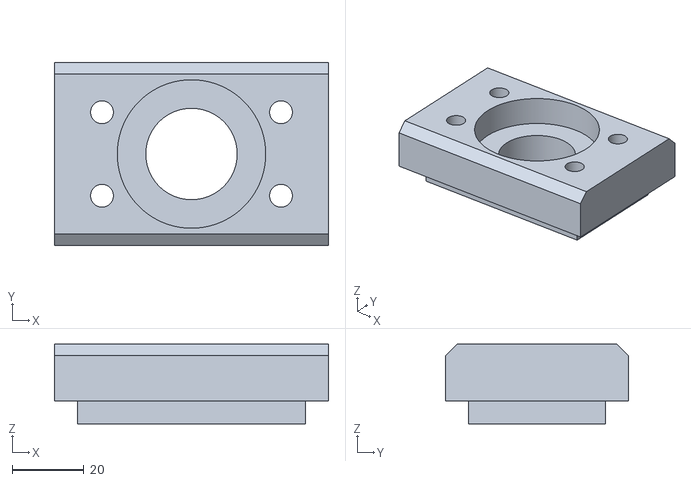
[picture p80: CAD file, 2020-08-20]
STLS/Done/2BearingSpacer^Forearm.STL
76.2 x 50.8 x 22.2
