evagorac/Terry/STLS/Done/1Body^J3Adapter_Shoulder.STL

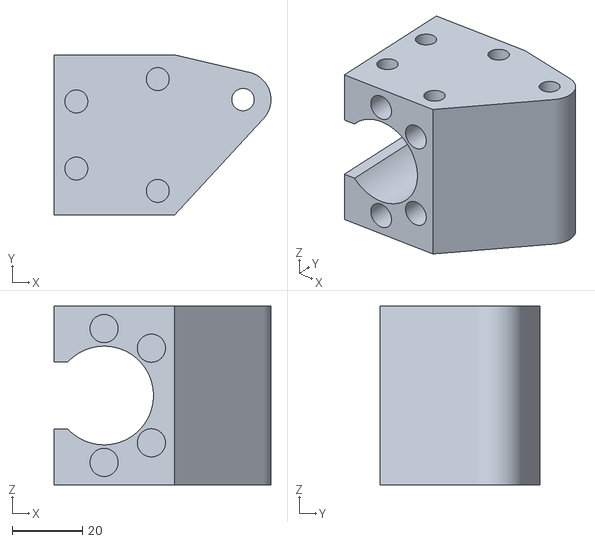
[picture p81: CAD file, 2020-08-20]
STLS/Done/1Body^J3Adapter_Shoulder.STL
61.6 x 45.5 x 50.8
