evagorac/Terry/STLS/Done/2Body^380kvMotorEncodedPlate.STL

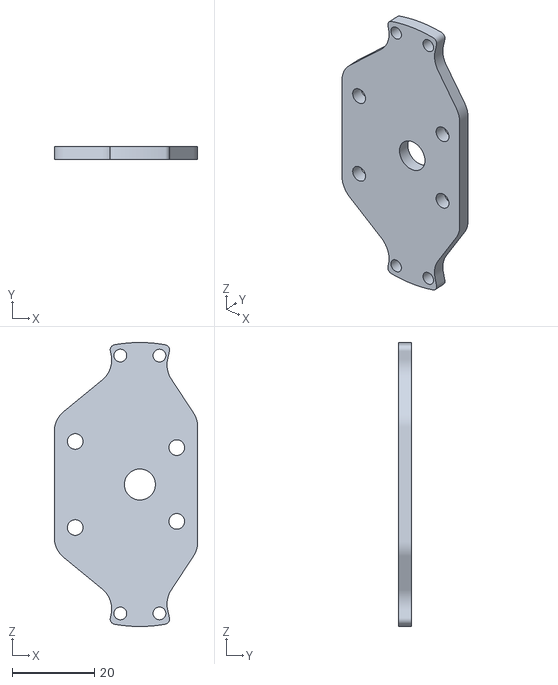
[picture p82: CAD file, 2020-08-20]
STLS/Done/2Body^380kvMotorEncodedPlate.STL
34.9 x 3.18 x 69.2
