evagorac/Terry/STLS/Done/2MirrorSideClamp.STL

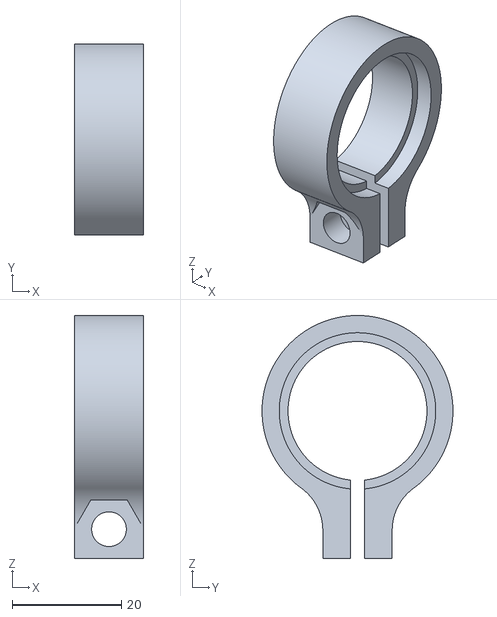
[picture p83: CAD file, 2020-08-20]
STLS/Done/2MirrorSideClamp.STL
12.7 x 34.9 x 44.5
