evagorac/Terry/STLS/Done/1Roller^TensionPillarJ2.STL

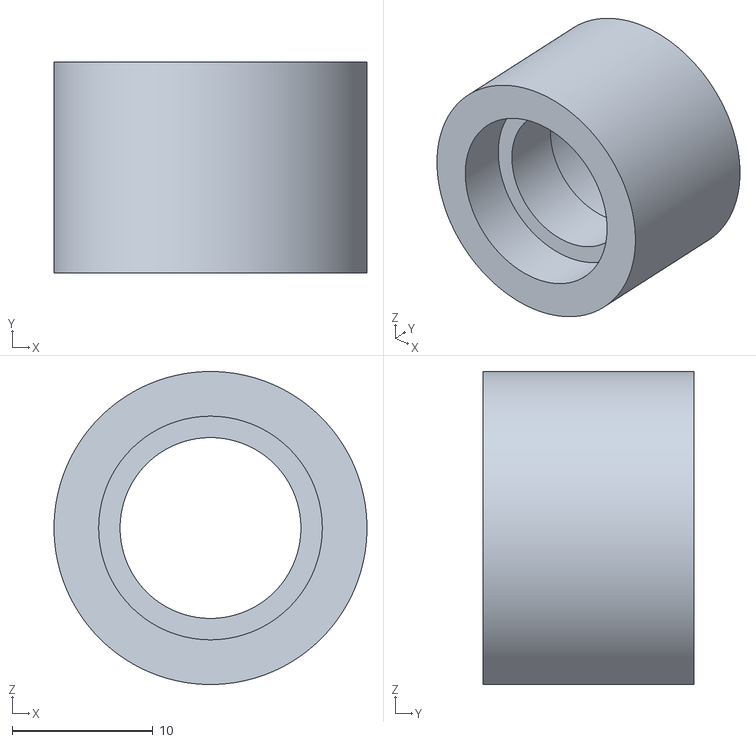
[picture p84: CAD file, 2020-08-20]
STLS/Done/1Roller^TensionPillarJ2.STL
22.2 x 15.0 x 22.2
