evagorac/Terry/STLS/Done/1J4SwitchMount^Forearm.STL

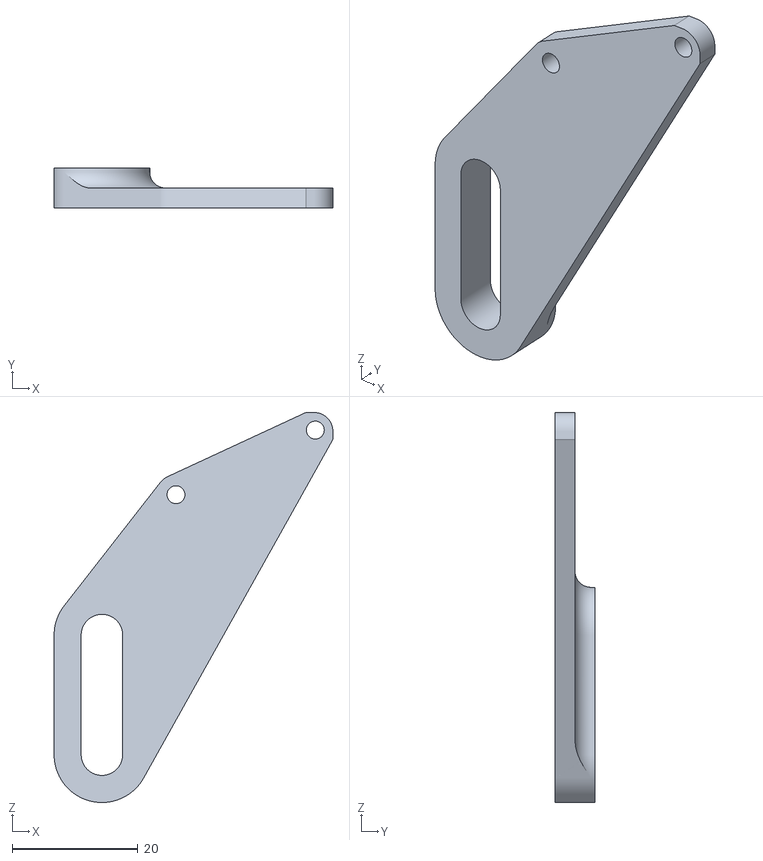
[picture p85: CAD file, 2020-08-20]
STLS/Done/1J4SwitchMount^Forearm.STL
44.4 x 6.35 x 62.1
