evagorac/Terry/STLS/Done/4Body^192kvMotorEncodedPlate.STL

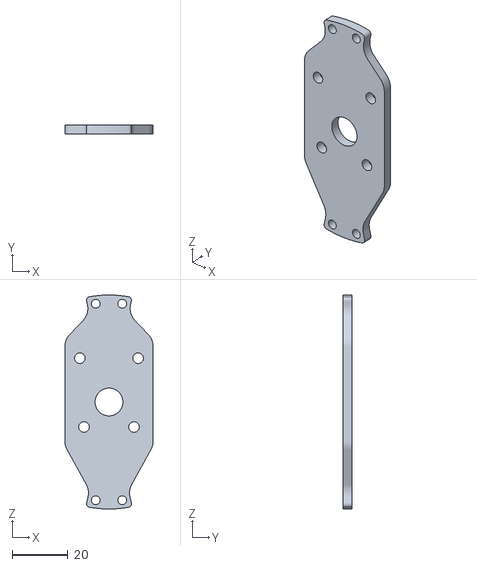
[picture p86: CAD file, 2020-08-20]
STLS/Done/4Body^192kvMotorEncodedPlate.STL
31.7 x 3.17 x 76.9
