evagorac/Terry/STLS/Done/1SwitchMountPlate^Shoulder.STL

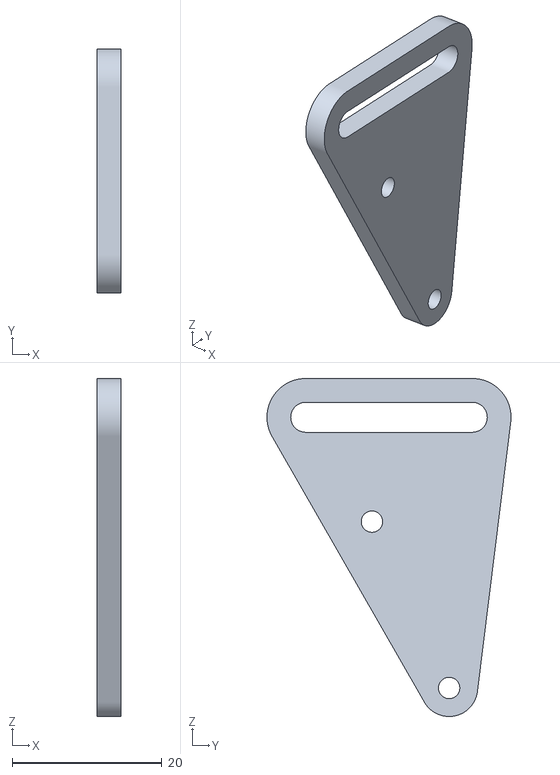
[picture p87: CAD file, 2020-08-20]
STLS/Done/1SwitchMountPlate^Shoulder.STL
3.17 x 32.6 x 45.1
