evagorac/Terry/STLS/Done/1BFSpacerWSwitchMount^Shoulder.STL

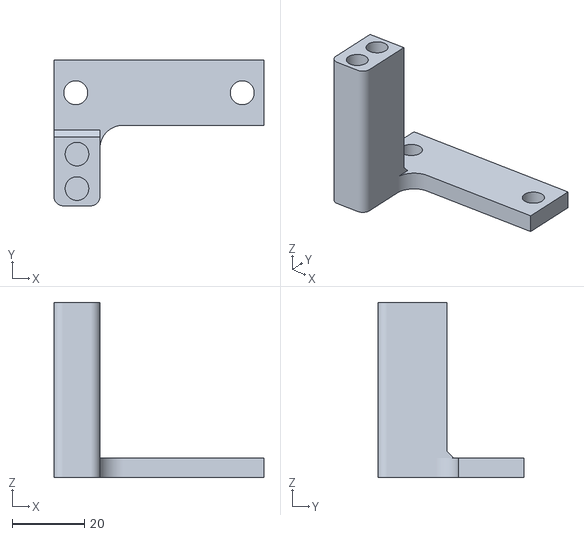
[picture p88: CAD file, 2020-08-20]
STLS/Done/1BFSpacerWSwitchMount^Shoulder.STL
58.0 x 40.2 x 48.4
