evagorac/Terry/STLS/Done/1J1SwitchMount^Base.STL

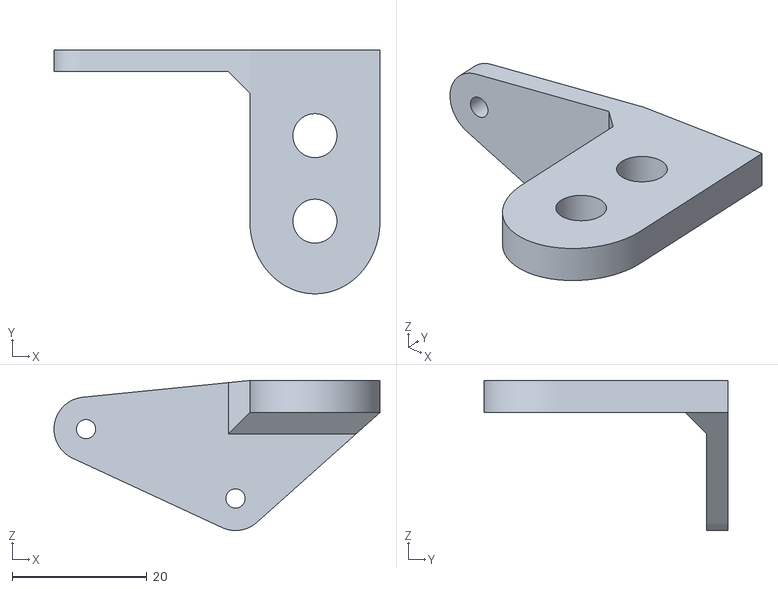
[picture p89: CAD file, 2020-08-20]
STLS/Done/1J1SwitchMount^Base.STL
48.4 x 36.2 x 22.3
