evagorac/Terry/STLS/Done/2KedaAdapter^Keda9to1.STL

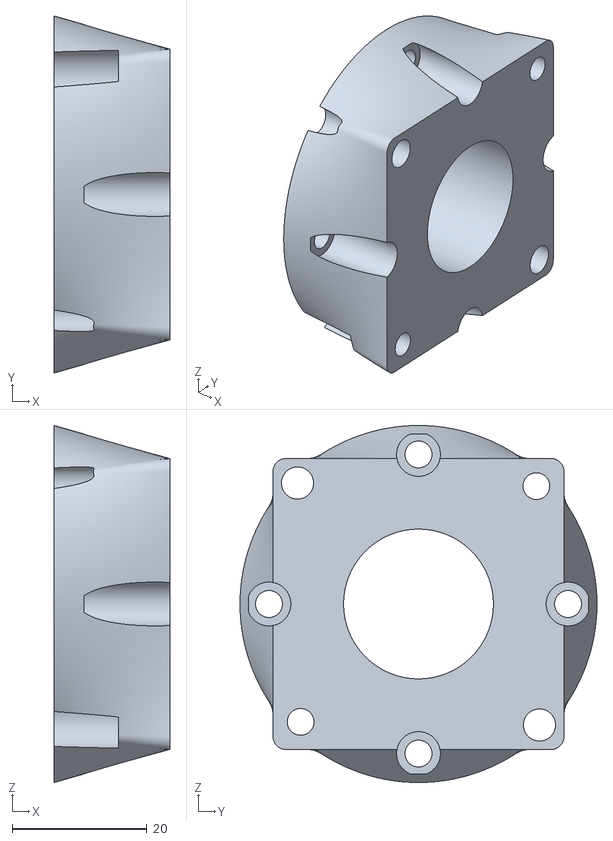
[picture p90: CAD file, 2020-08-20]
STLS/Done/2KedaAdapter^Keda9to1.STL
17.2 x 53.0 x 53.0
