evagorac/Terry/STLS/Done/1J6Trigger^Forearm.STL

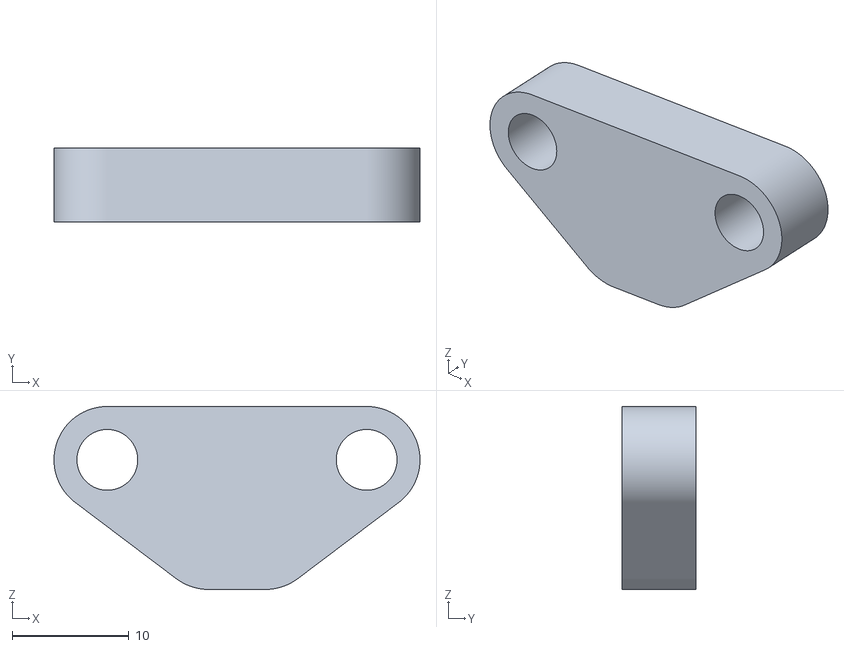
[picture p91: CAD file, 2020-08-20]
STLS/Done/1J6Trigger^Forearm.STL
31.4 x 6.35 x 15.7
