evagorac/Terry/STLS/Done/1TensionConnector^Base.STL

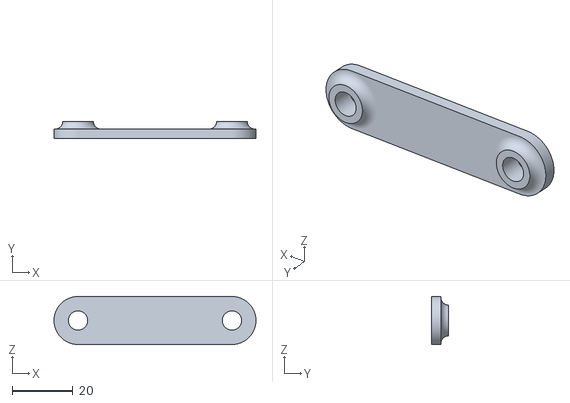
[picture p92: CAD file, 2020-08-20]
STLS/Done/1TensionConnector^Base.STL
66.7 x 5.72 x 15.9
