evagorac/Terry/STLS/Done/2SidePulleySpacer^Forearm.STL

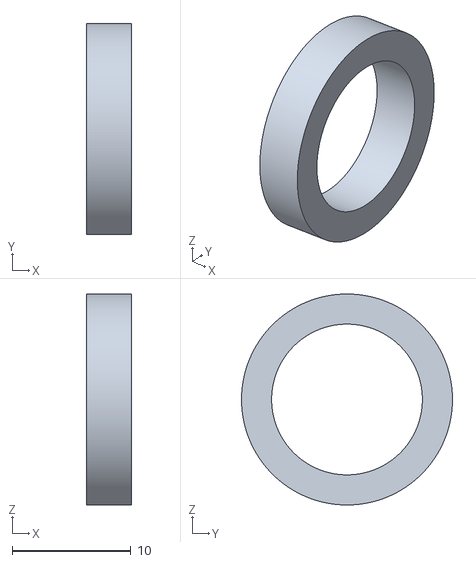
[picture p93: CAD file, 2020-08-20]
STLS/Done/2SidePulleySpacer^Forearm.STL
3.81 x 17.8 x 17.8
