evagorac/Terry/STLS/Done/2PDAdapter^PropDrive10to1.STL

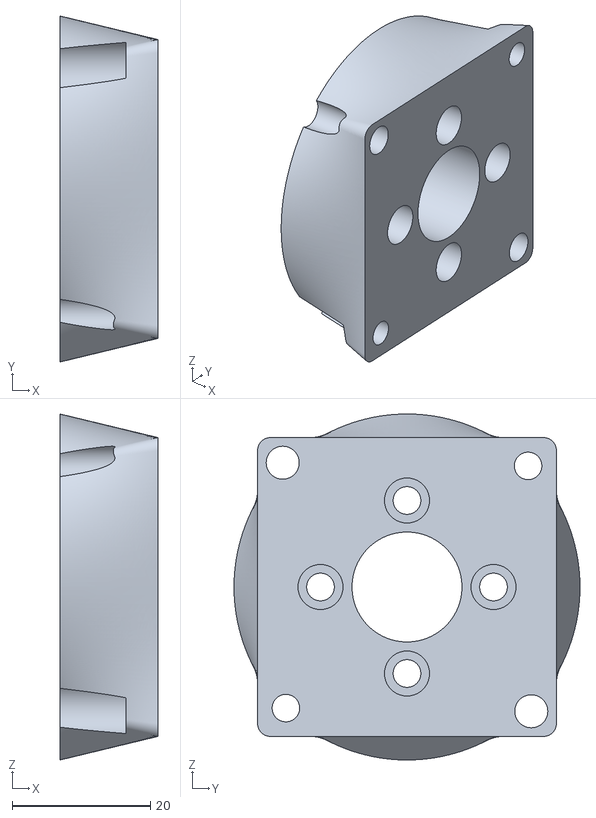
[picture p94: CAD file, 2020-08-20]
STLS/Done/2PDAdapter^PropDrive10to1.STL
14.1 x 50.0 x 50.0
