evagorac/Terry/STLS/Done/2Roller^TensionPillarJ1.STL

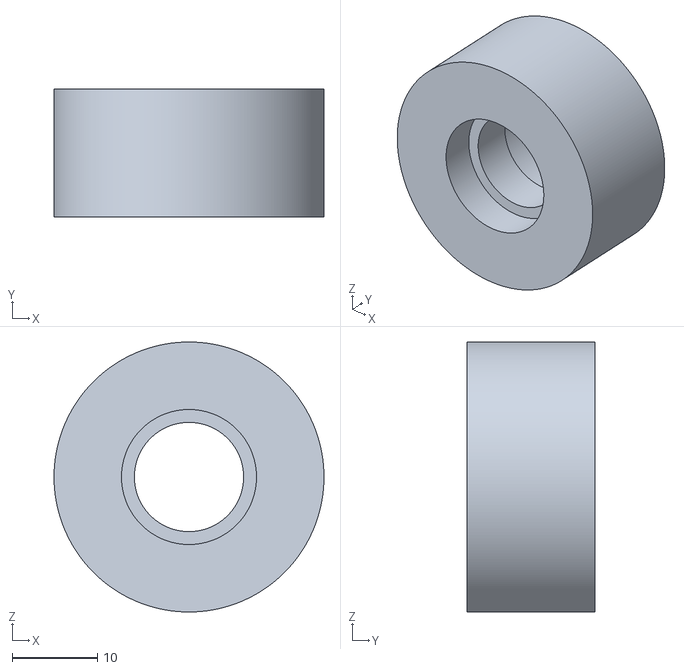
[picture p95: CAD file, 2020-08-20]
STLS/Done/2Roller^TensionPillarJ1.STL
31.7 x 15.0 x 31.8
