evagorac/Terry/STLS/Done/2Roller^TensionPillarJ56.STL

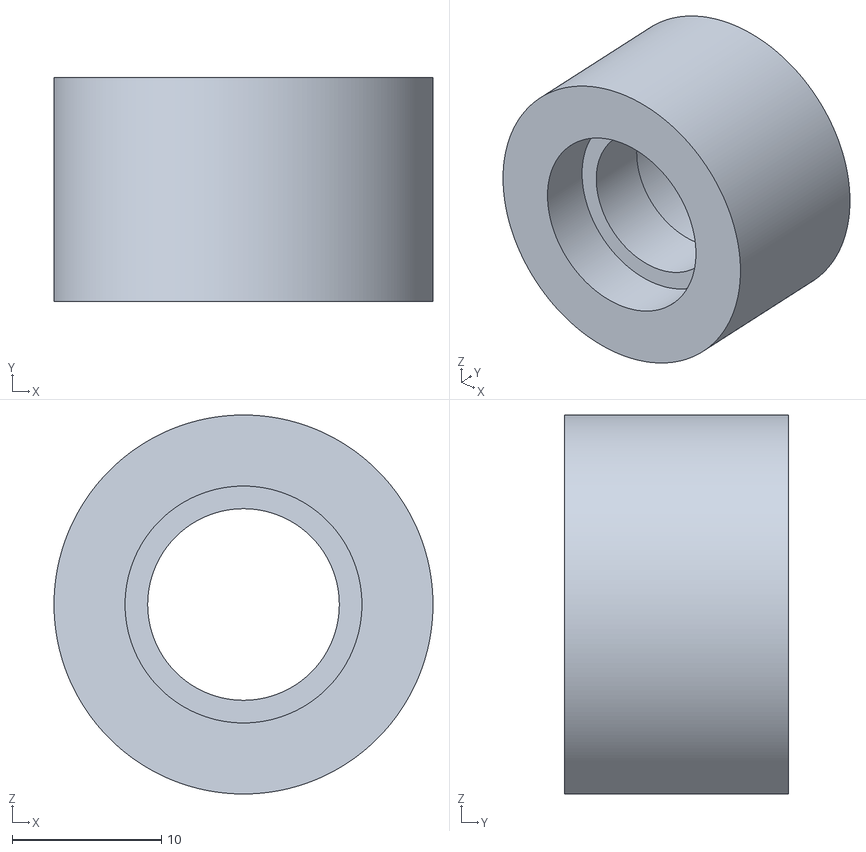
[picture p96: CAD file, 2020-08-20]
STLS/Done/2Roller^TensionPillarJ56.STL
25.4 x 15.0 x 25.4
