evagorac/Terry/STLS/Done/1SwitchMount^Shoulder.STL

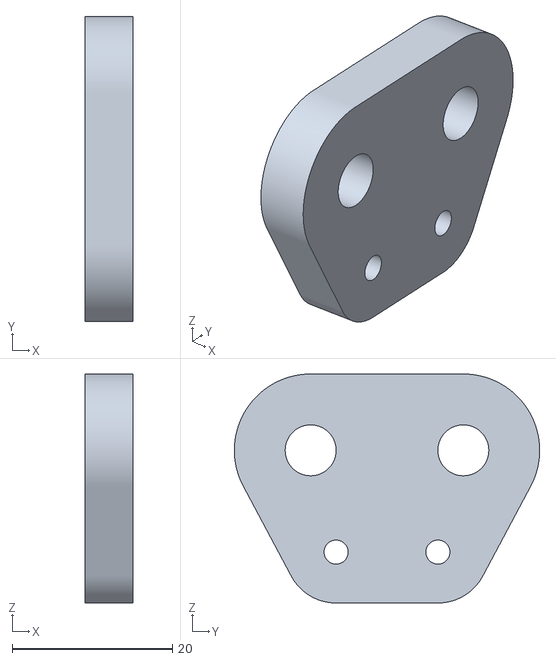
[picture p97: CAD file, 2020-08-20]
STLS/Done/1SwitchMount^Shoulder.STL
6.00 x 38.1 x 28.6
