evagorac/Terry/STLS/Done/3MiterSpacer^Forearm.STL

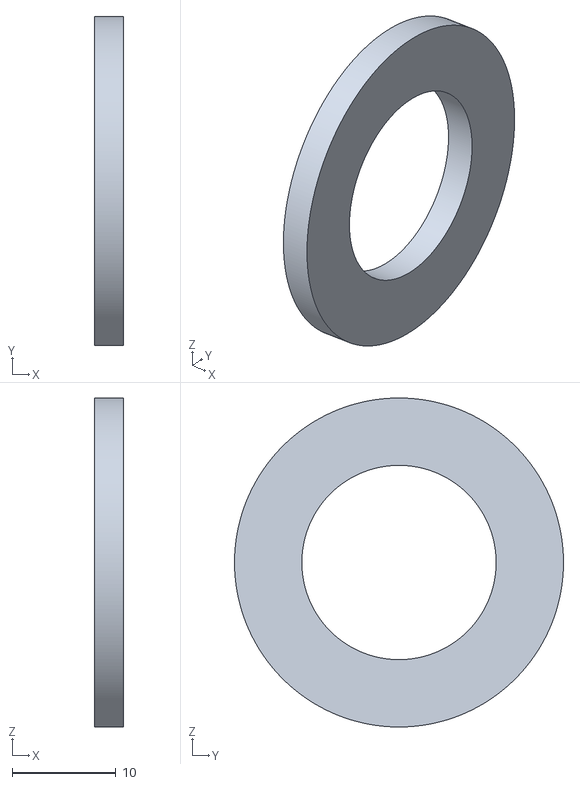
[picture p98: CAD file, 2020-08-20]
STLS/Done/3MiterSpacer^Forearm.STL
2.82 x 31.8 x 31.8
