evagorac/Terry/STLS/Done/2Body^380kvMotorEncoded.STL

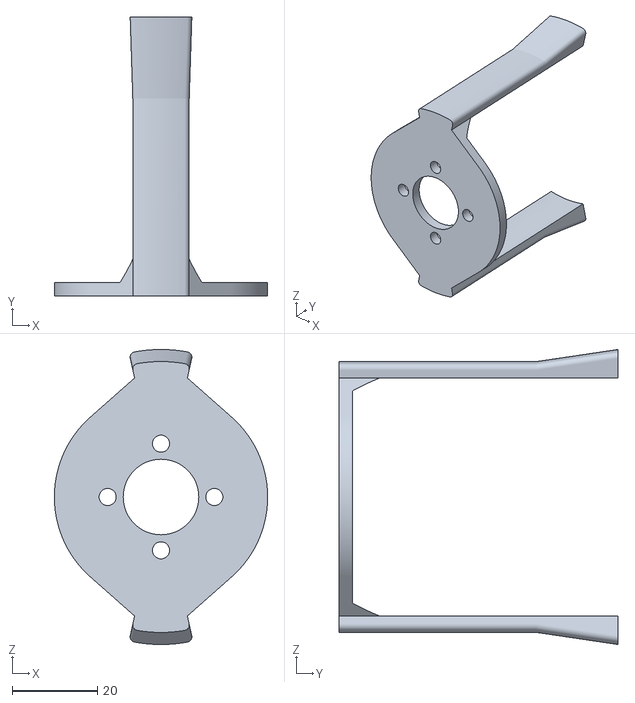
[picture p99: CAD file, 2020-08-20]
STLS/Done/2Body^380kvMotorEncoded.STL
50.0 x 65.3 x 69.1
