evagorac/Terry/STLS/Done/2SidePrintedSupport^Forearm.STL

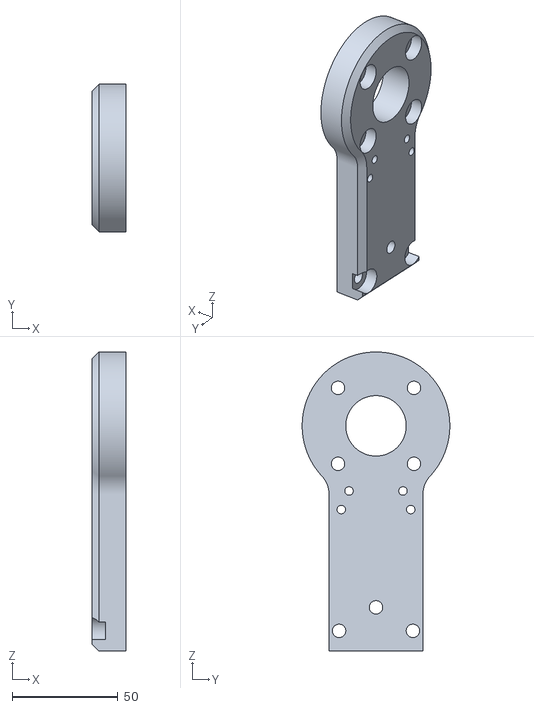
[picture p100: CAD file, 2020-08-20]
STLS/Done/2SidePrintedSupport^Forearm.STL
15.9 x 69.8 x 141.4
